74th/ch32v-dev-boards/ch32v203-promicro/docs/ch32v203-promicro.png

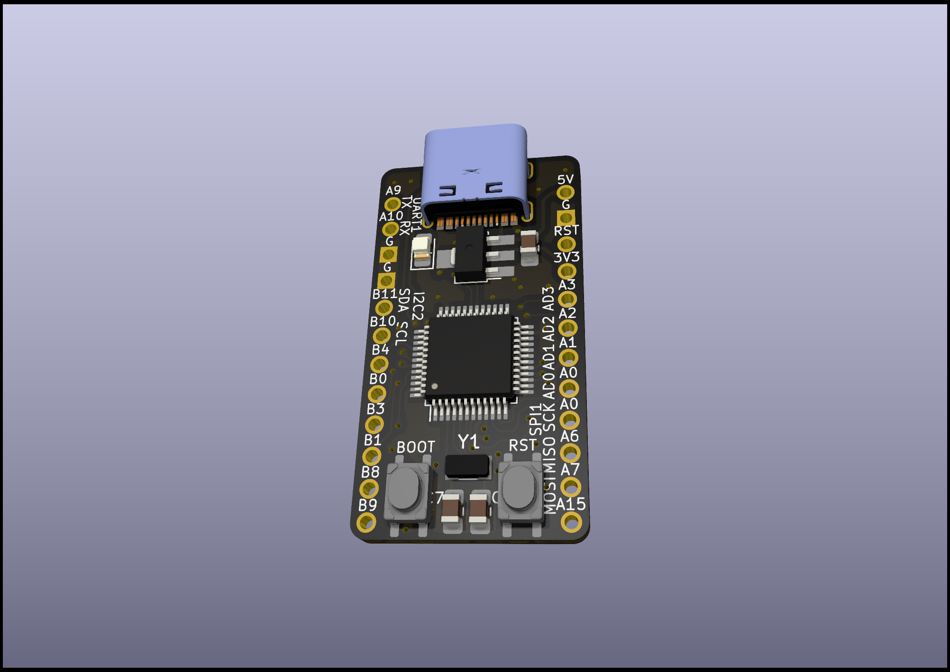
ch32v203-promicro/docs/ch32v203-promicro.png
