74th/ch32v-dev-boards/ch32v203-promicro/docs/switch-science/74th-ch32v203-promicro-like-photo1.jpg

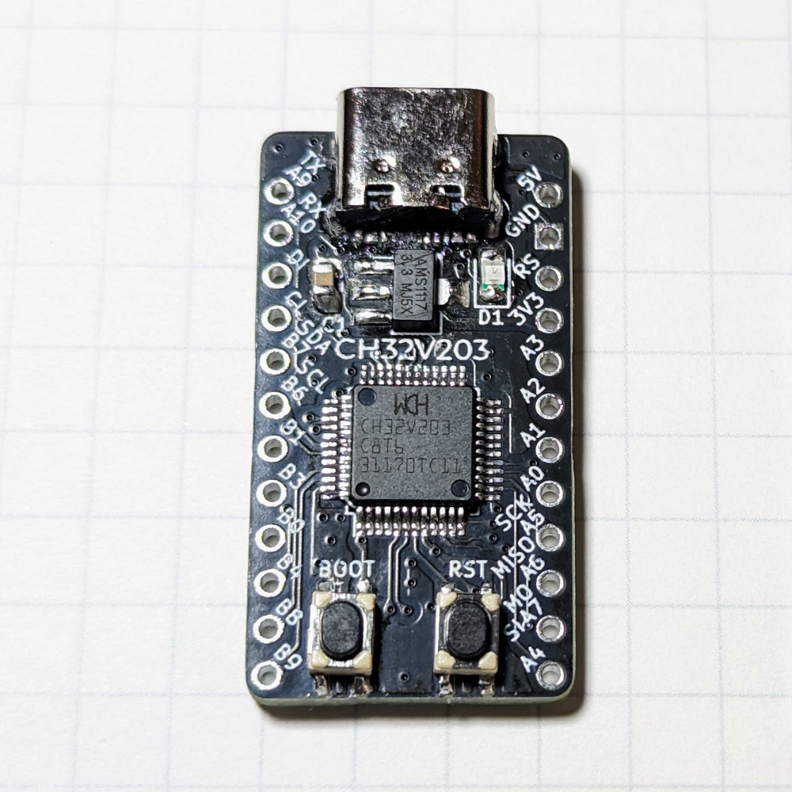
ch32v203-promicro/docs/switch-science/74th-ch32v203-promicro-like-photo1.jpg
