74th/ch32v-dev-boards/ch32v203-promicro/docs/x32micro-v1.1.0-pcb.pdf

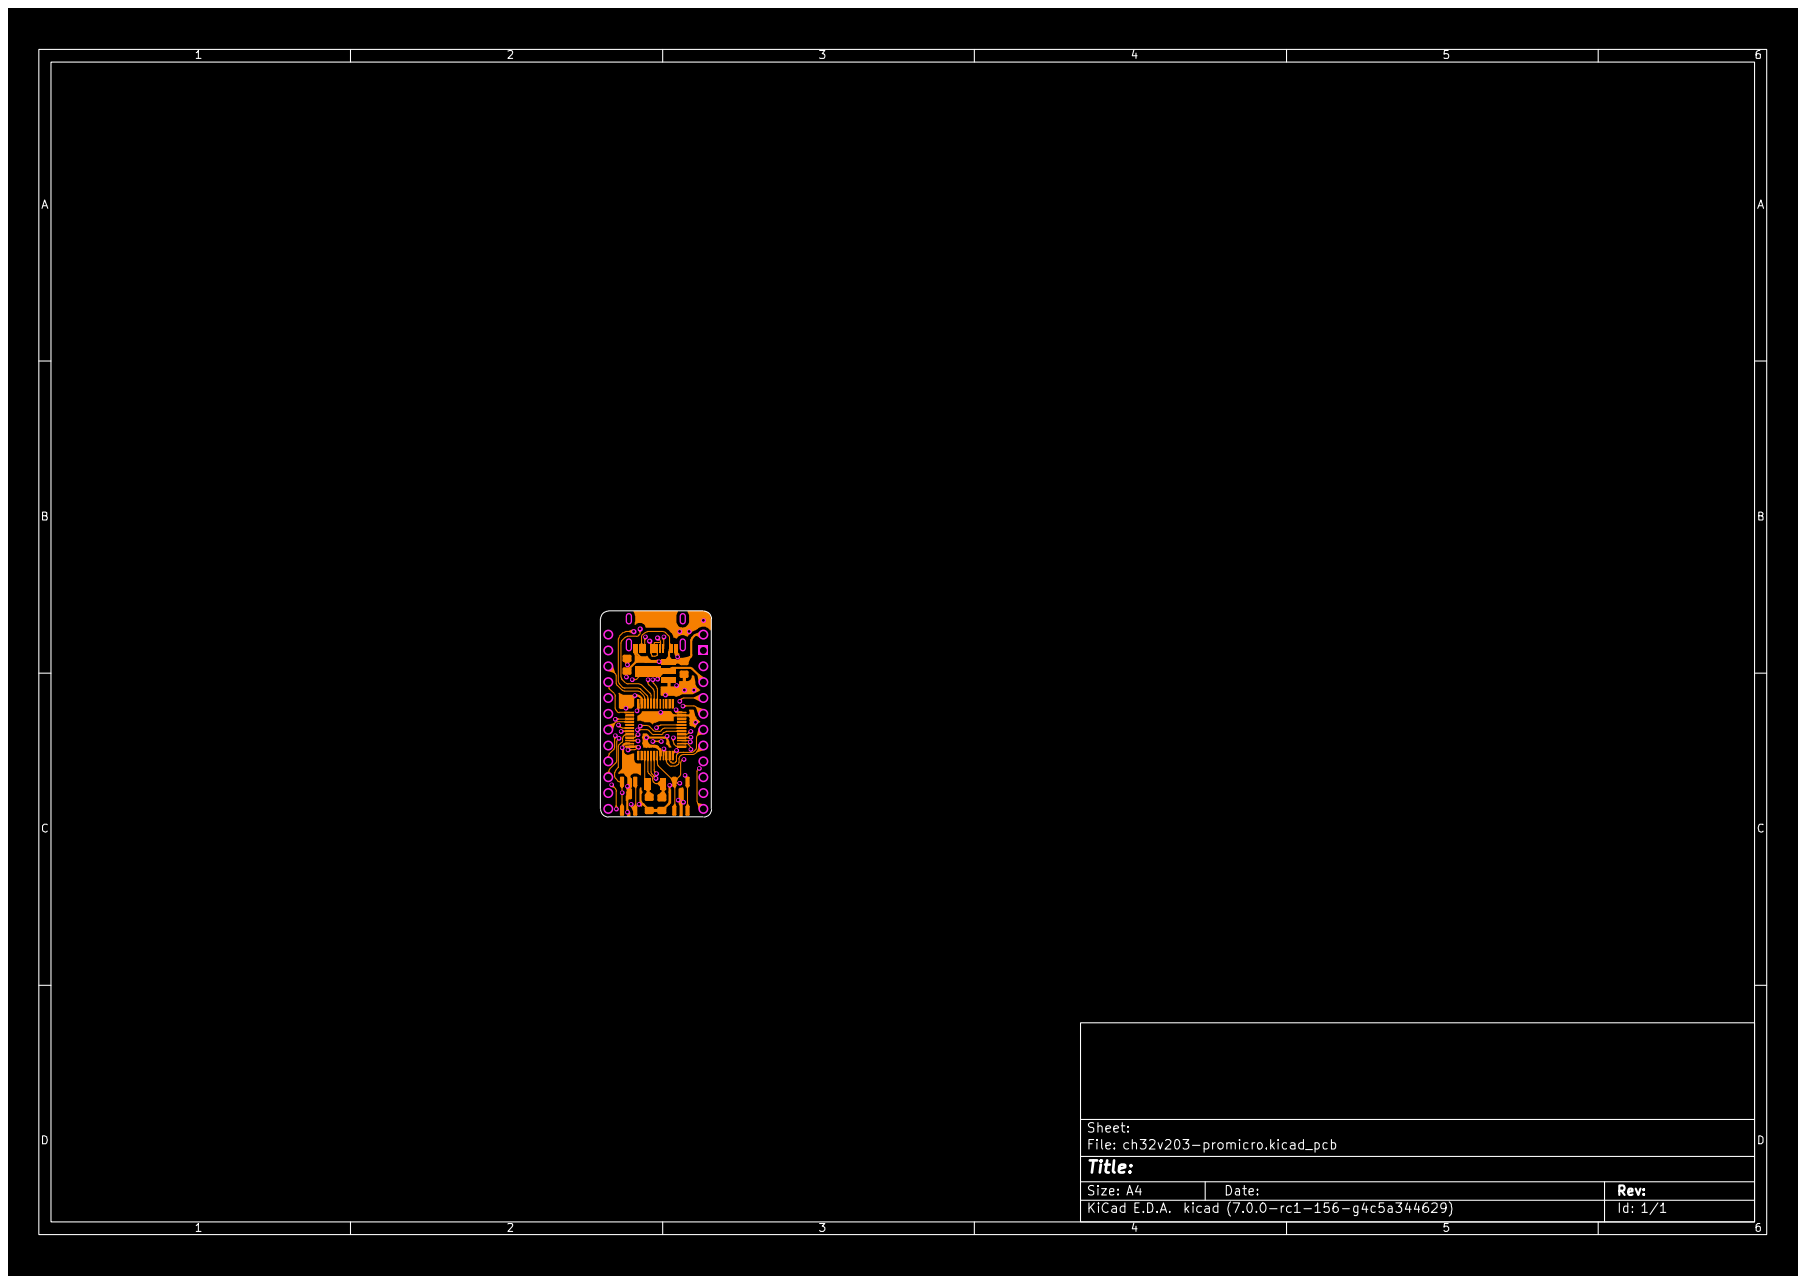
[picture p43: page 1]

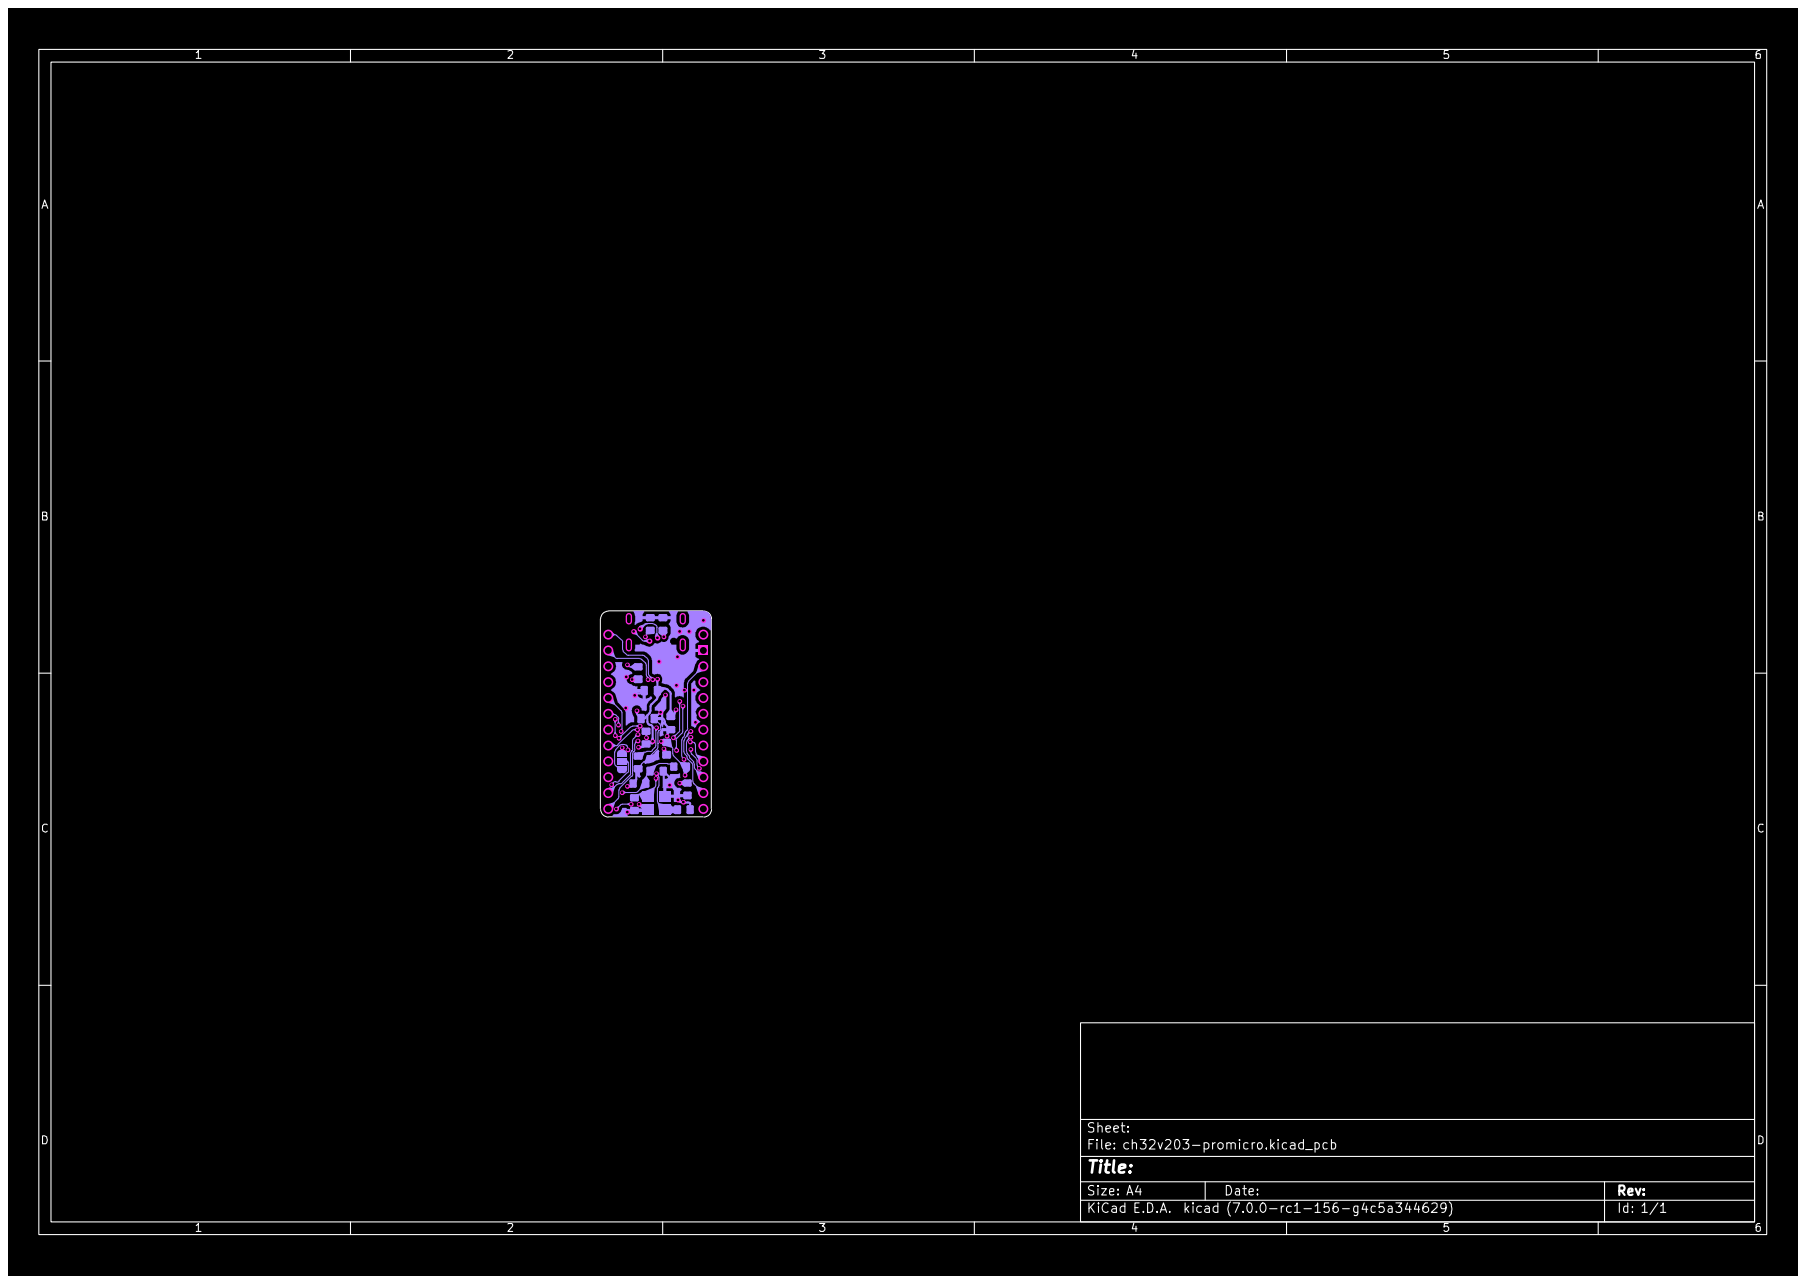
[picture p44: page 2]

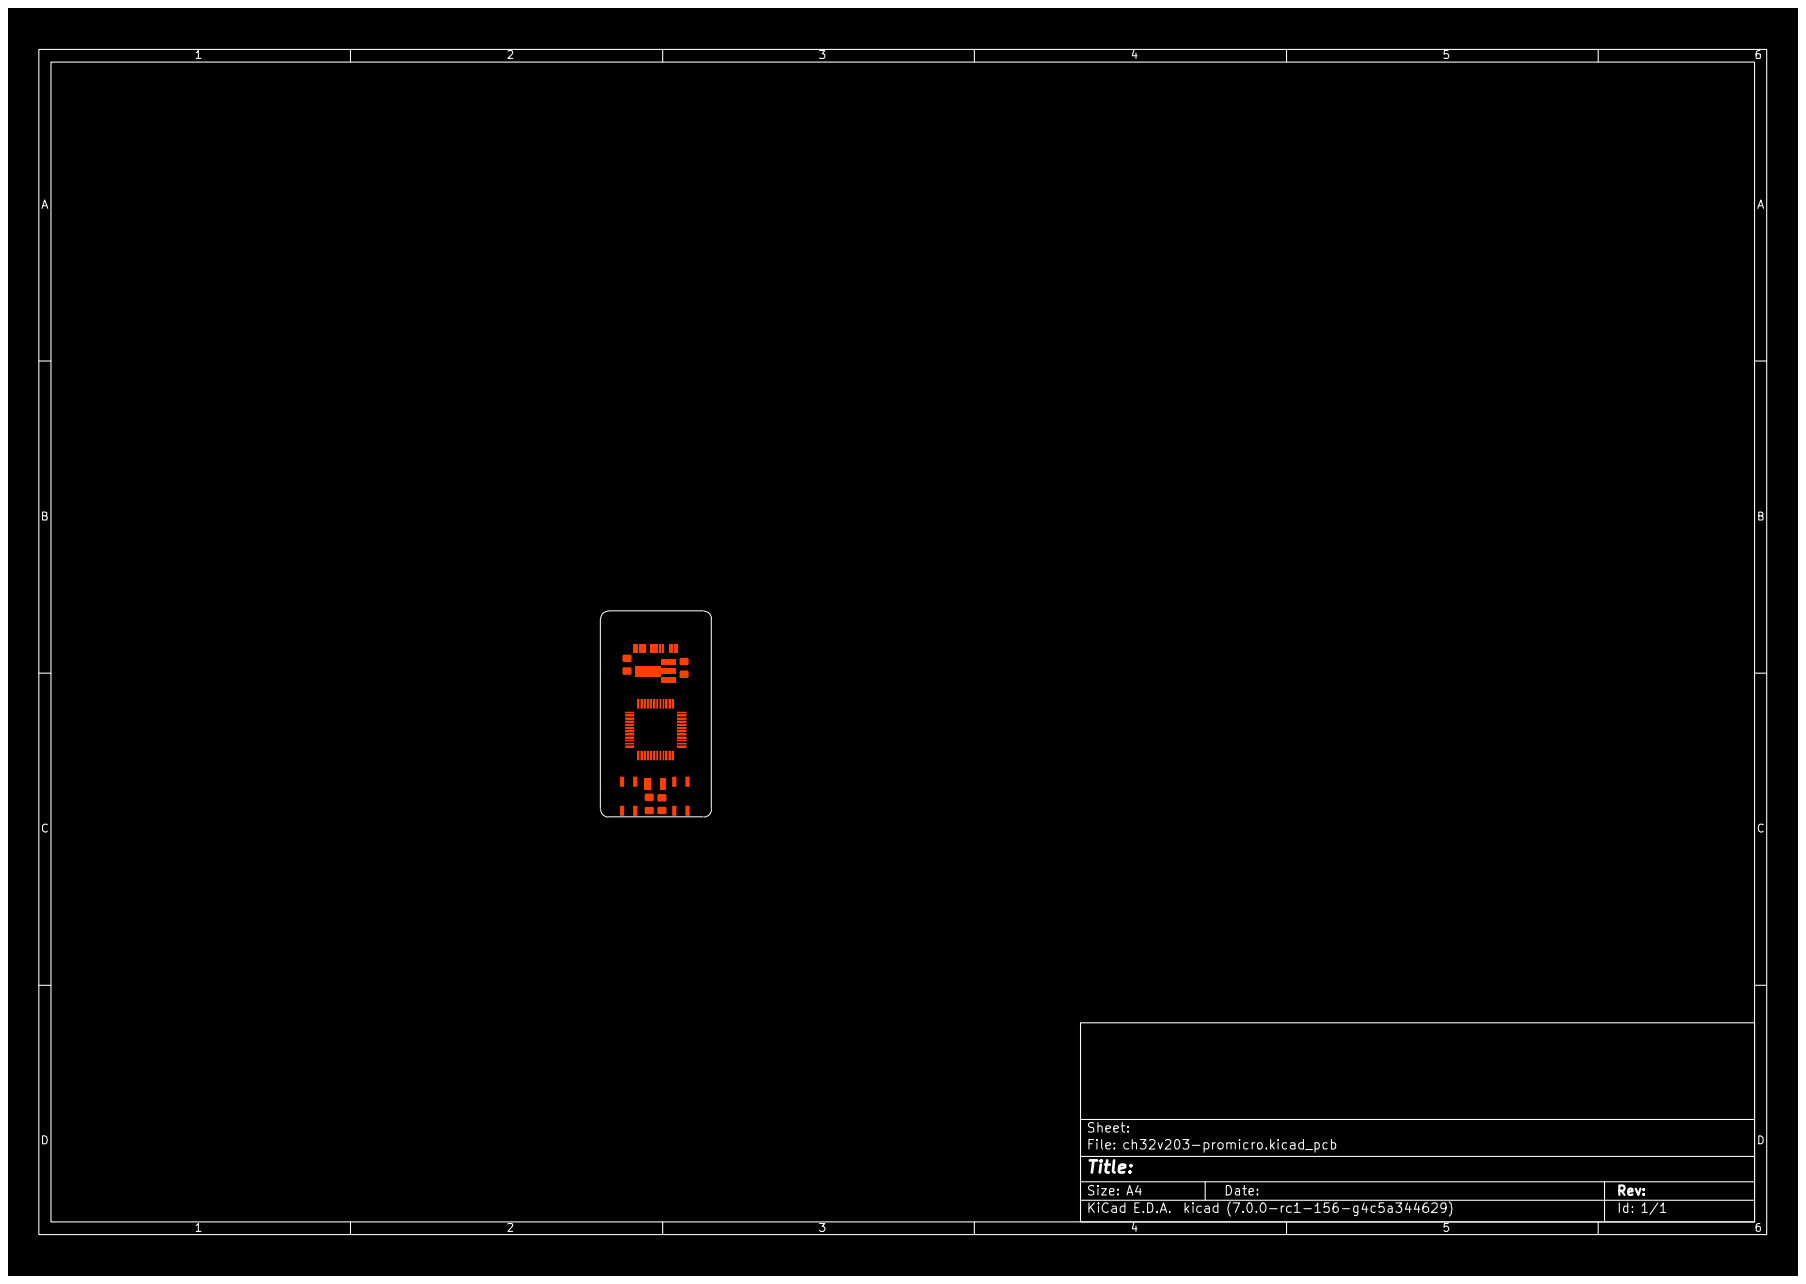
[picture p45: page 3]

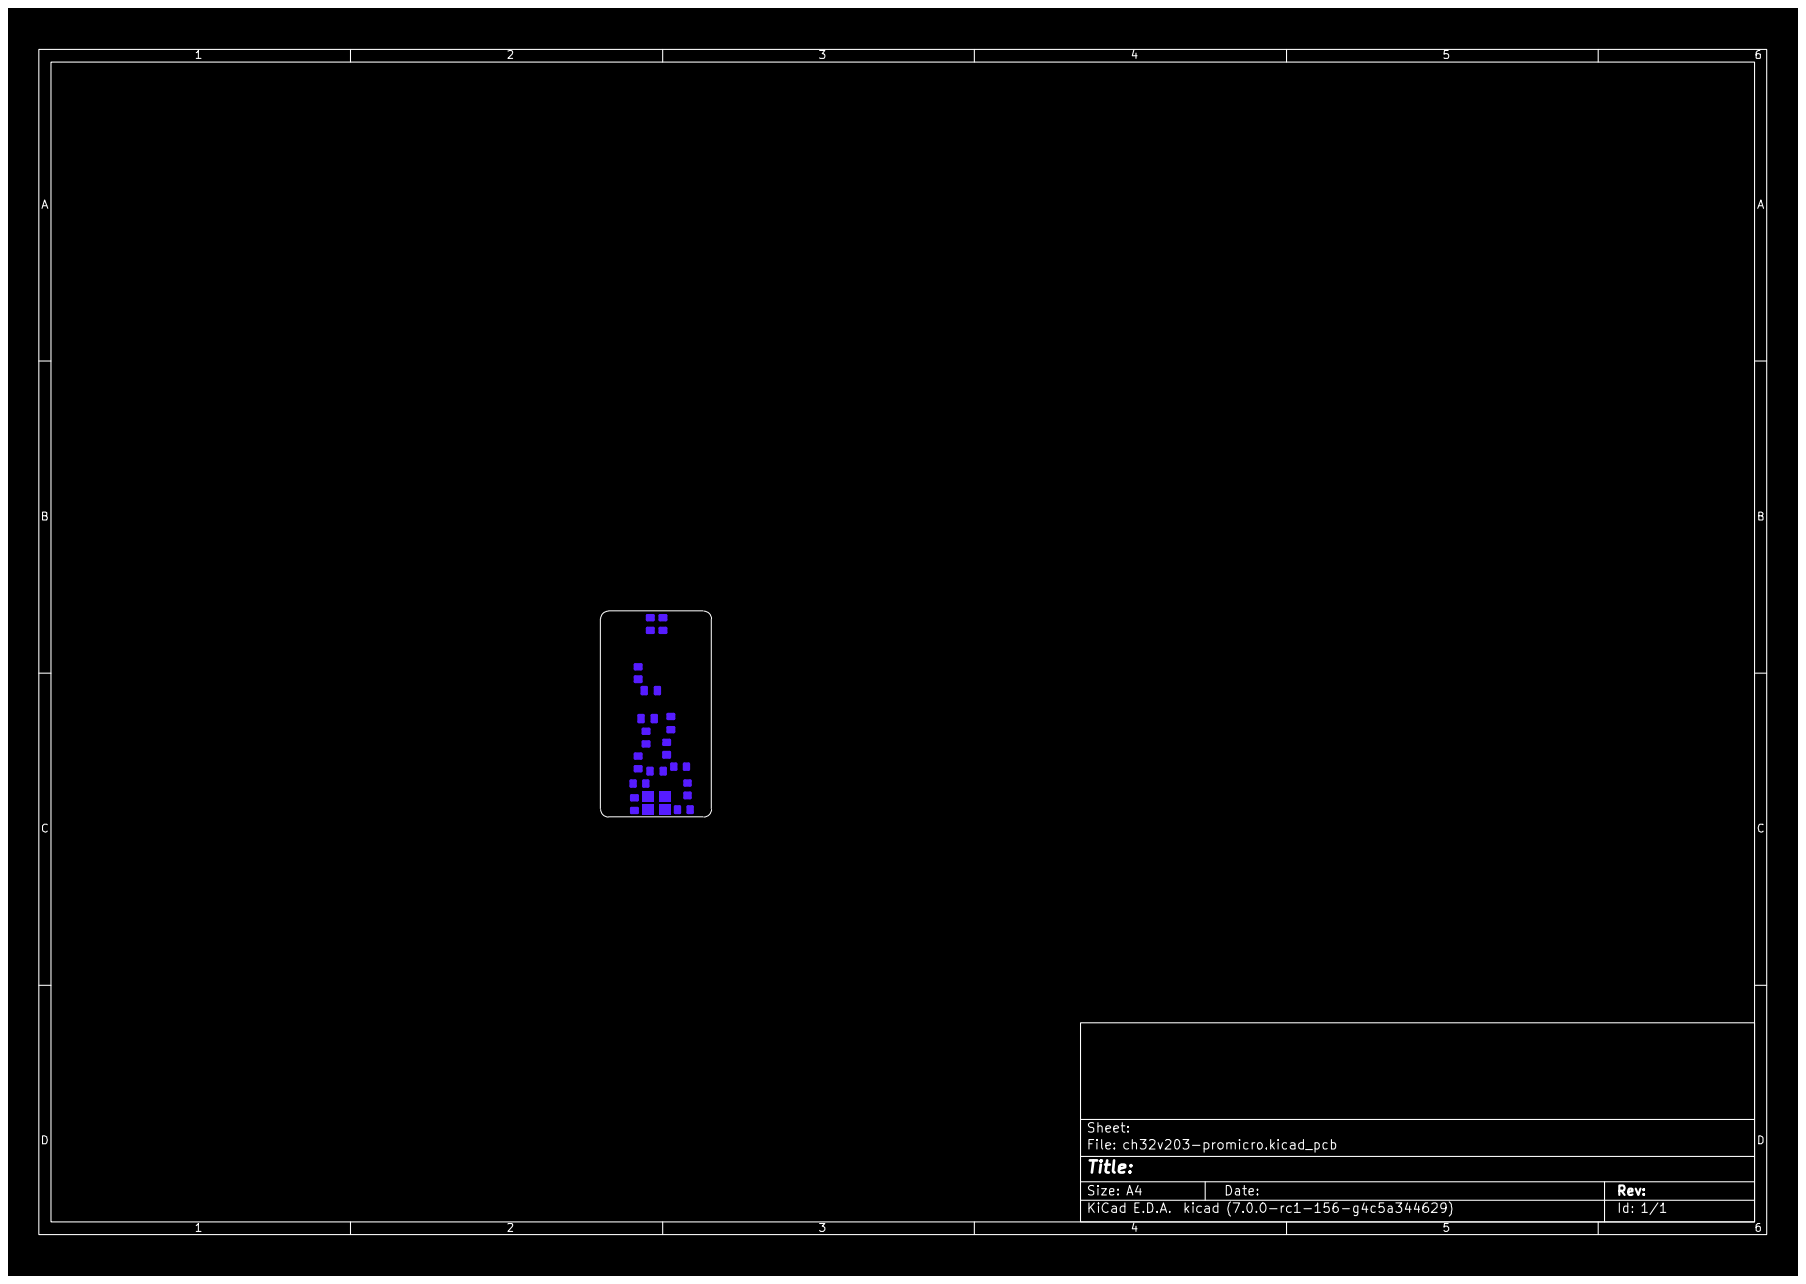
[picture p46: page 4]

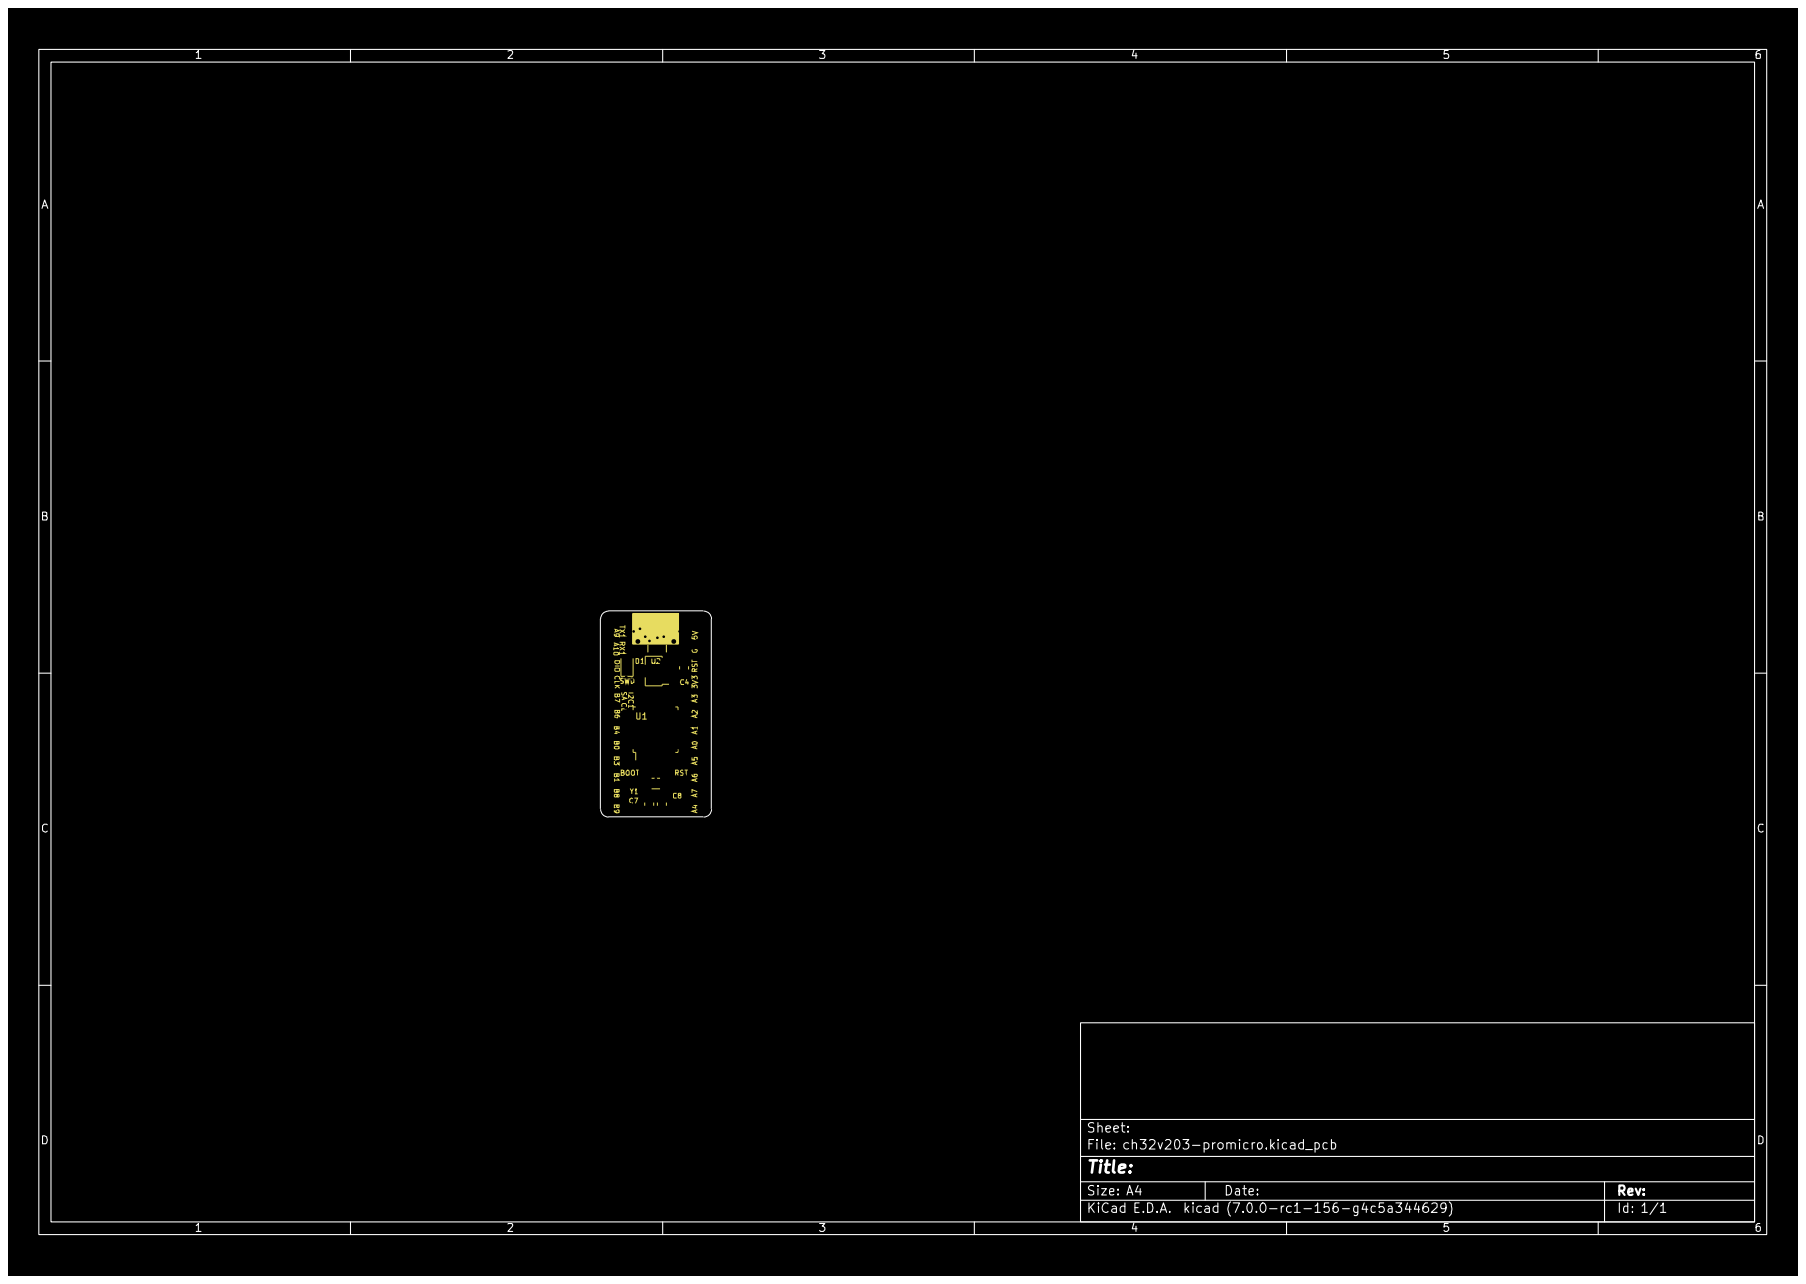
[picture p47: page 5]

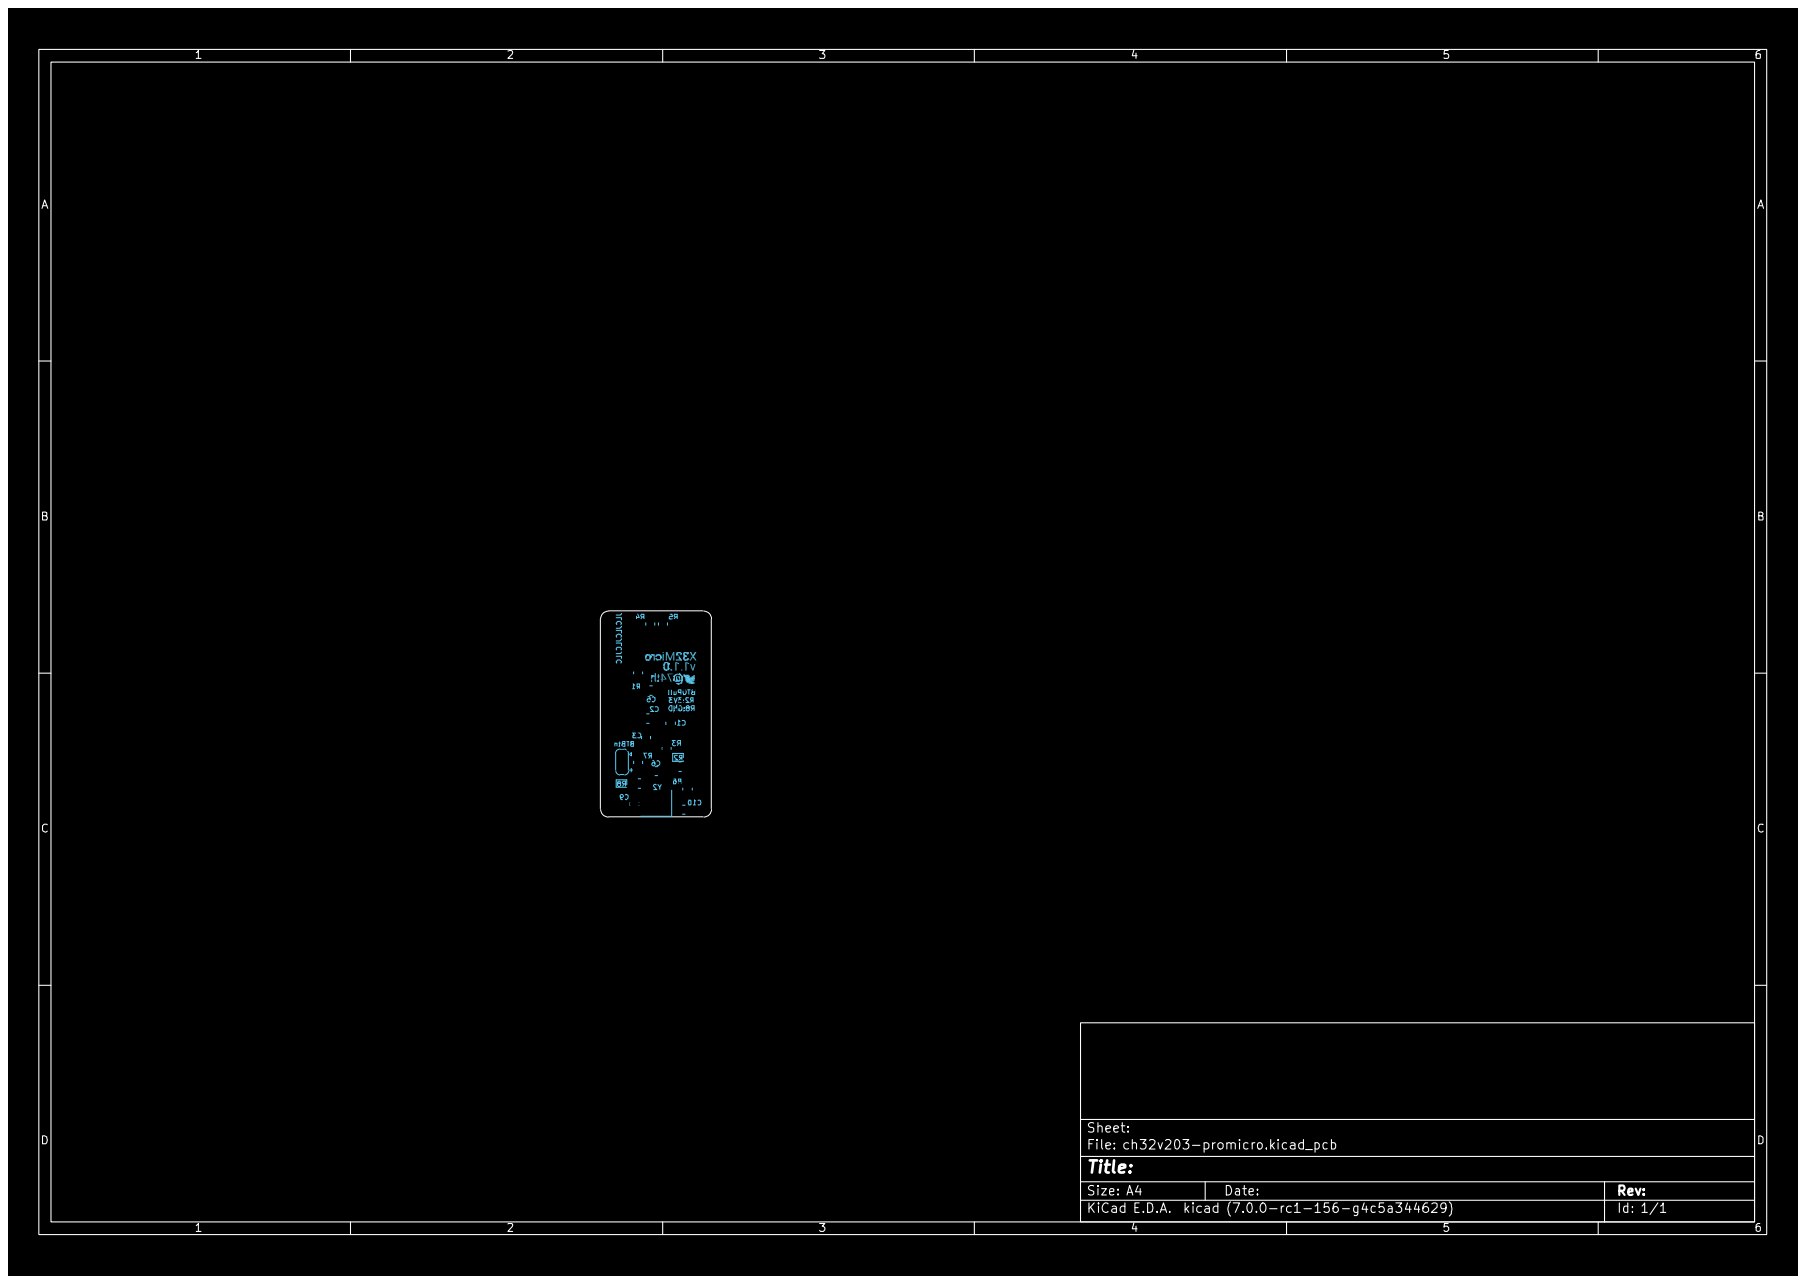
[picture p48: page 6]

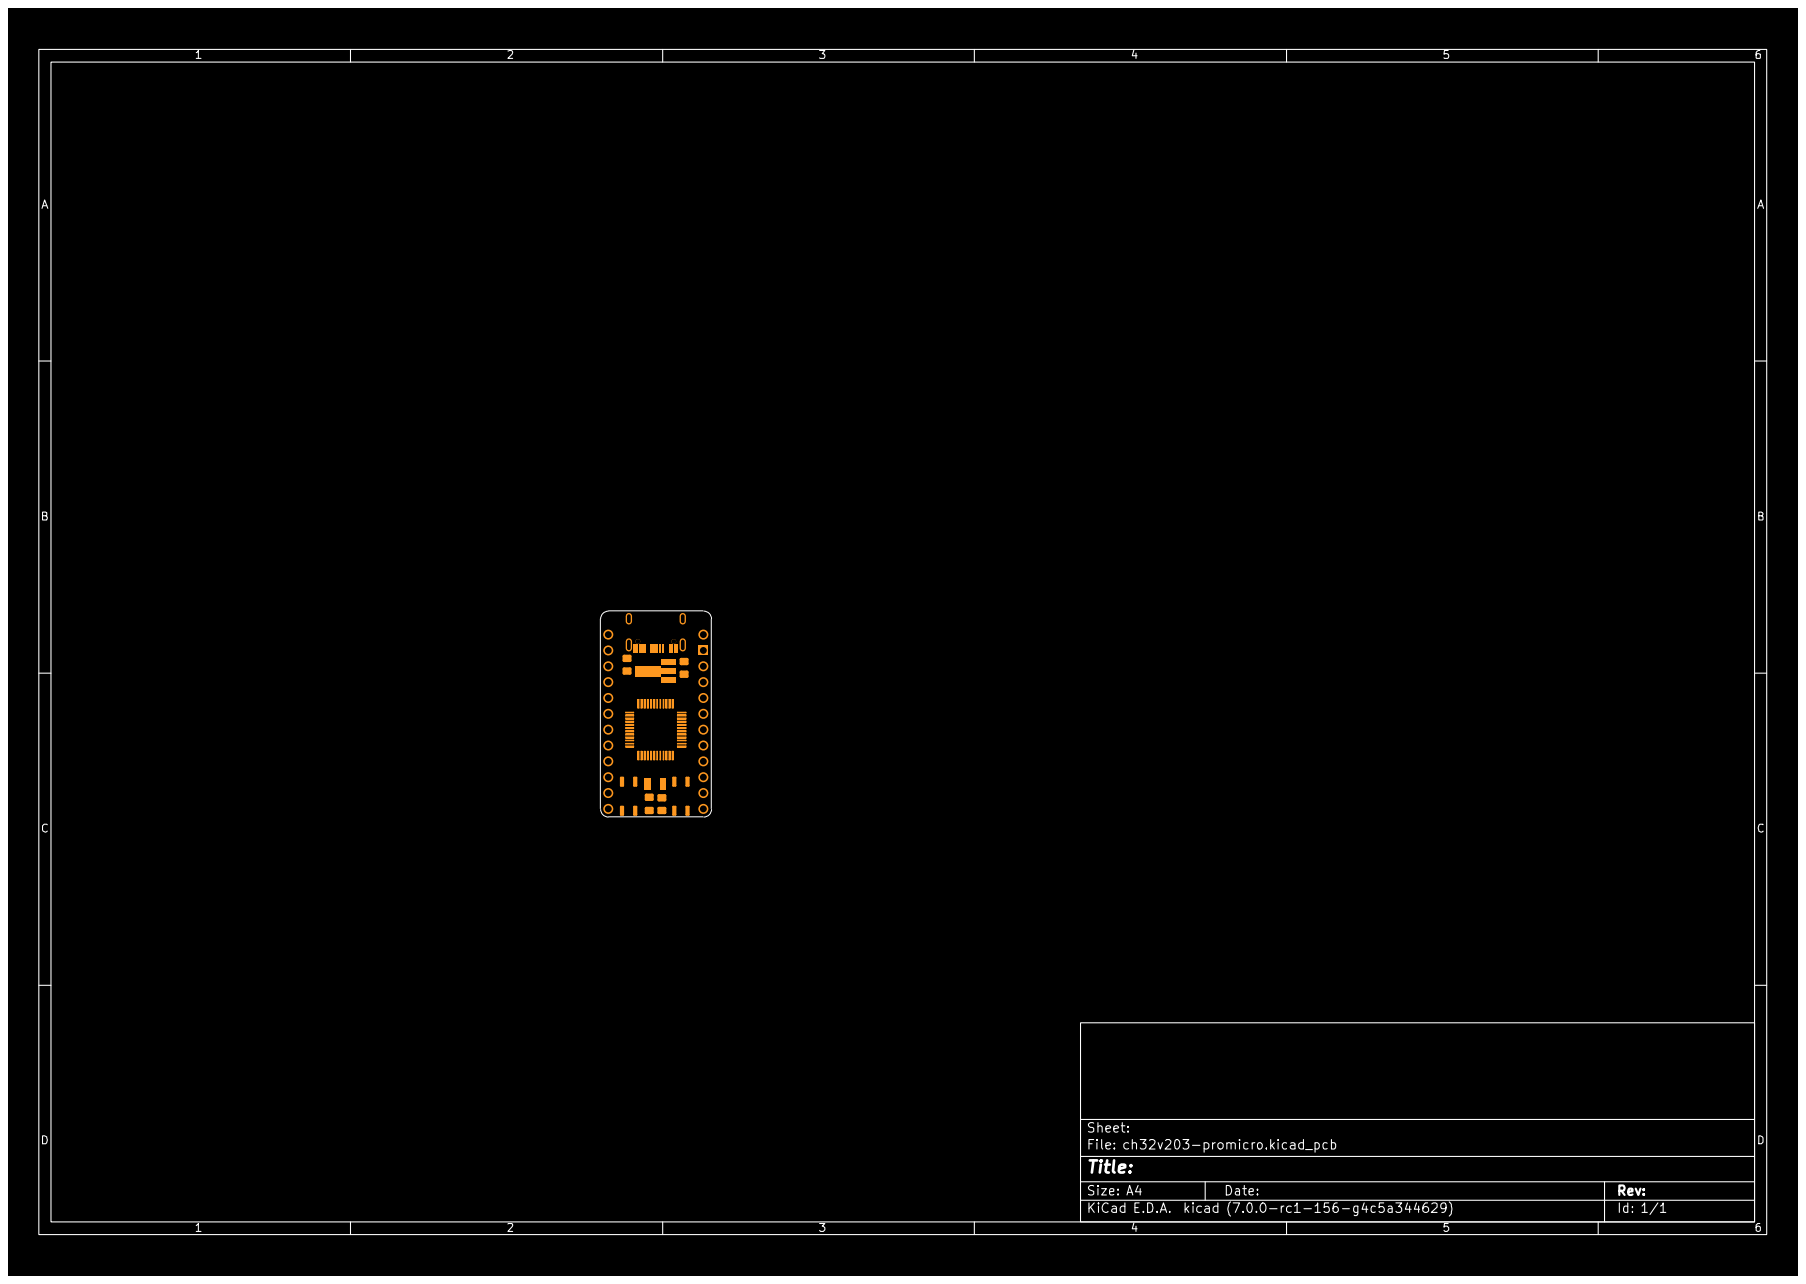
[picture p49: page 7]

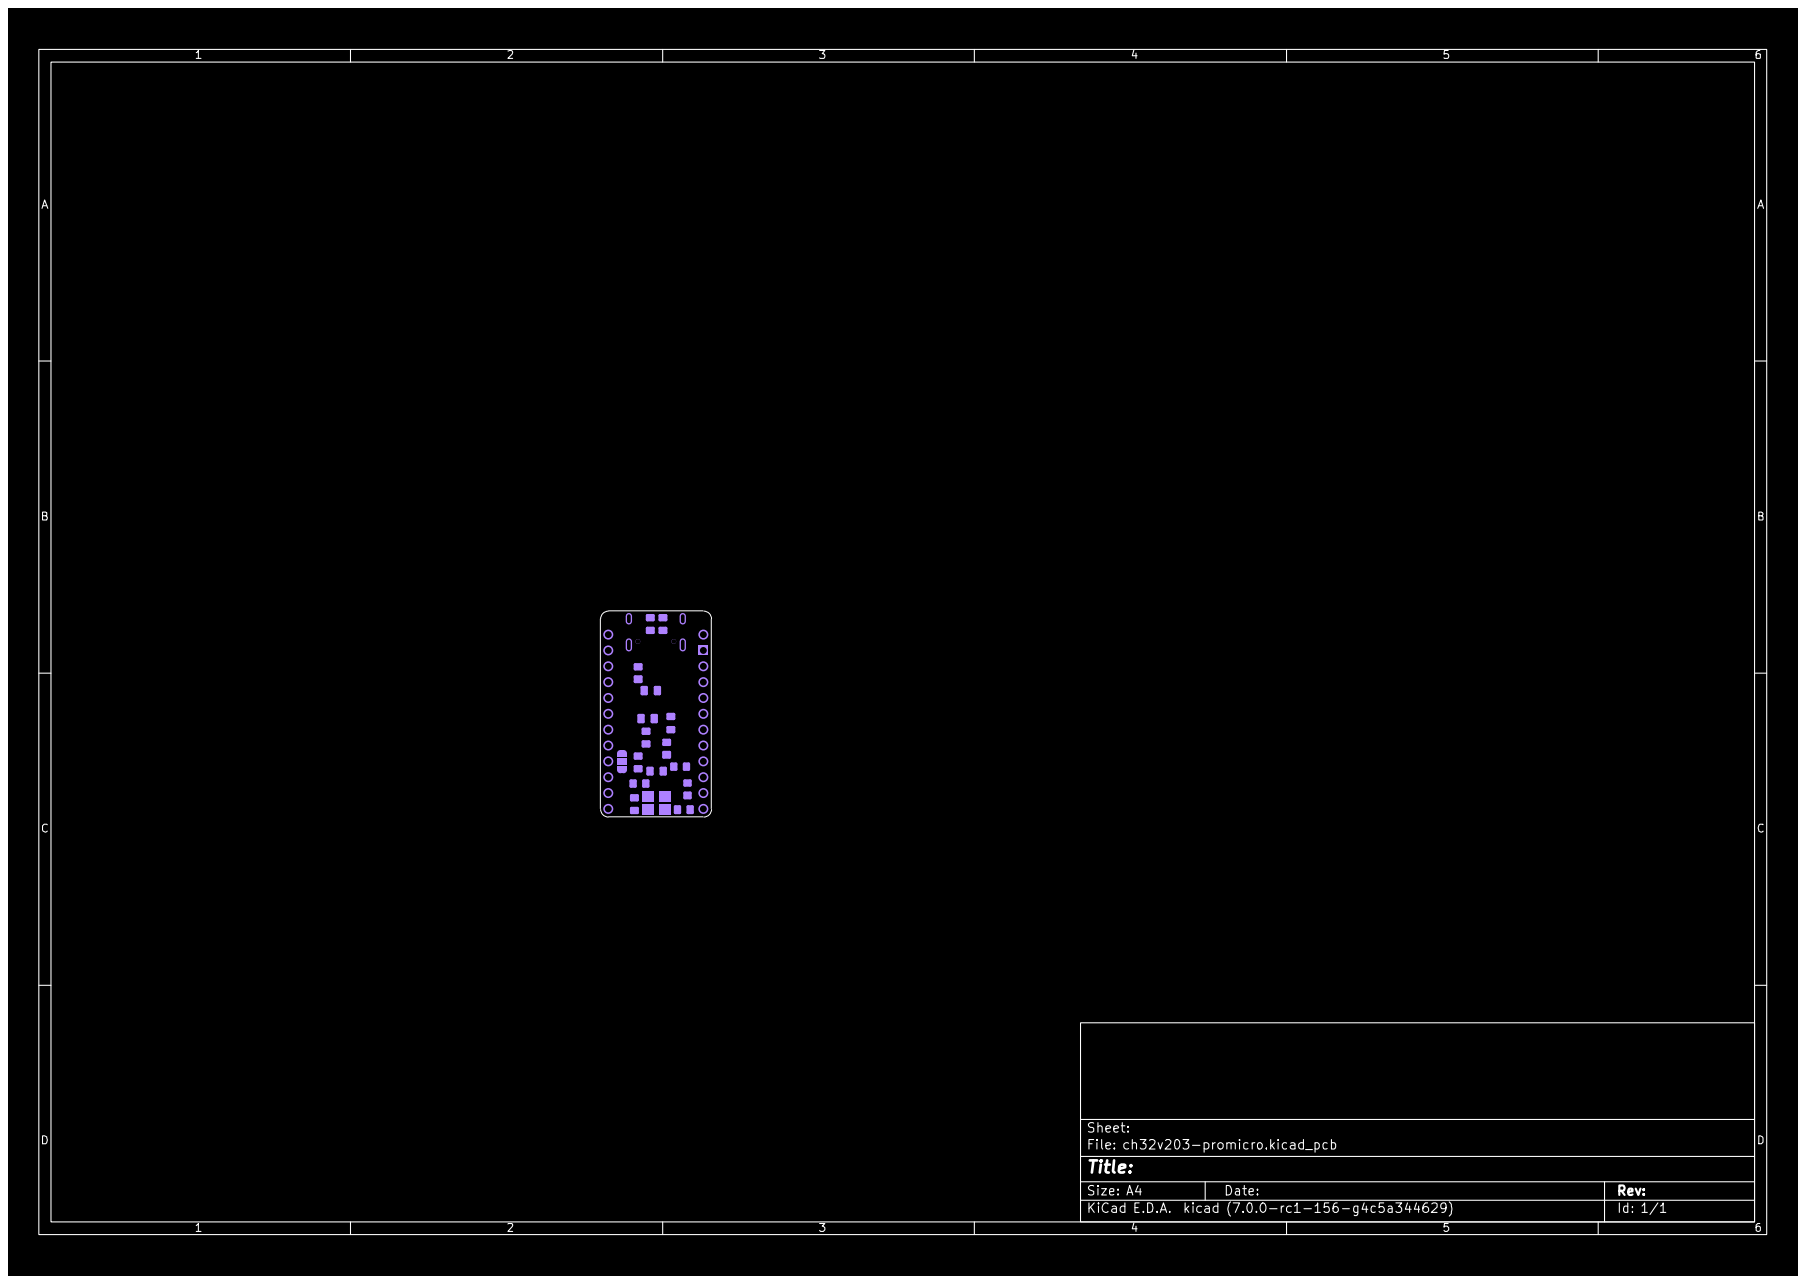
[picture p50: page 8]
