74th/ch32v-dev-boards/ch32v203-promicro/docs/x32micro-v1.1.0-semantics.pdf

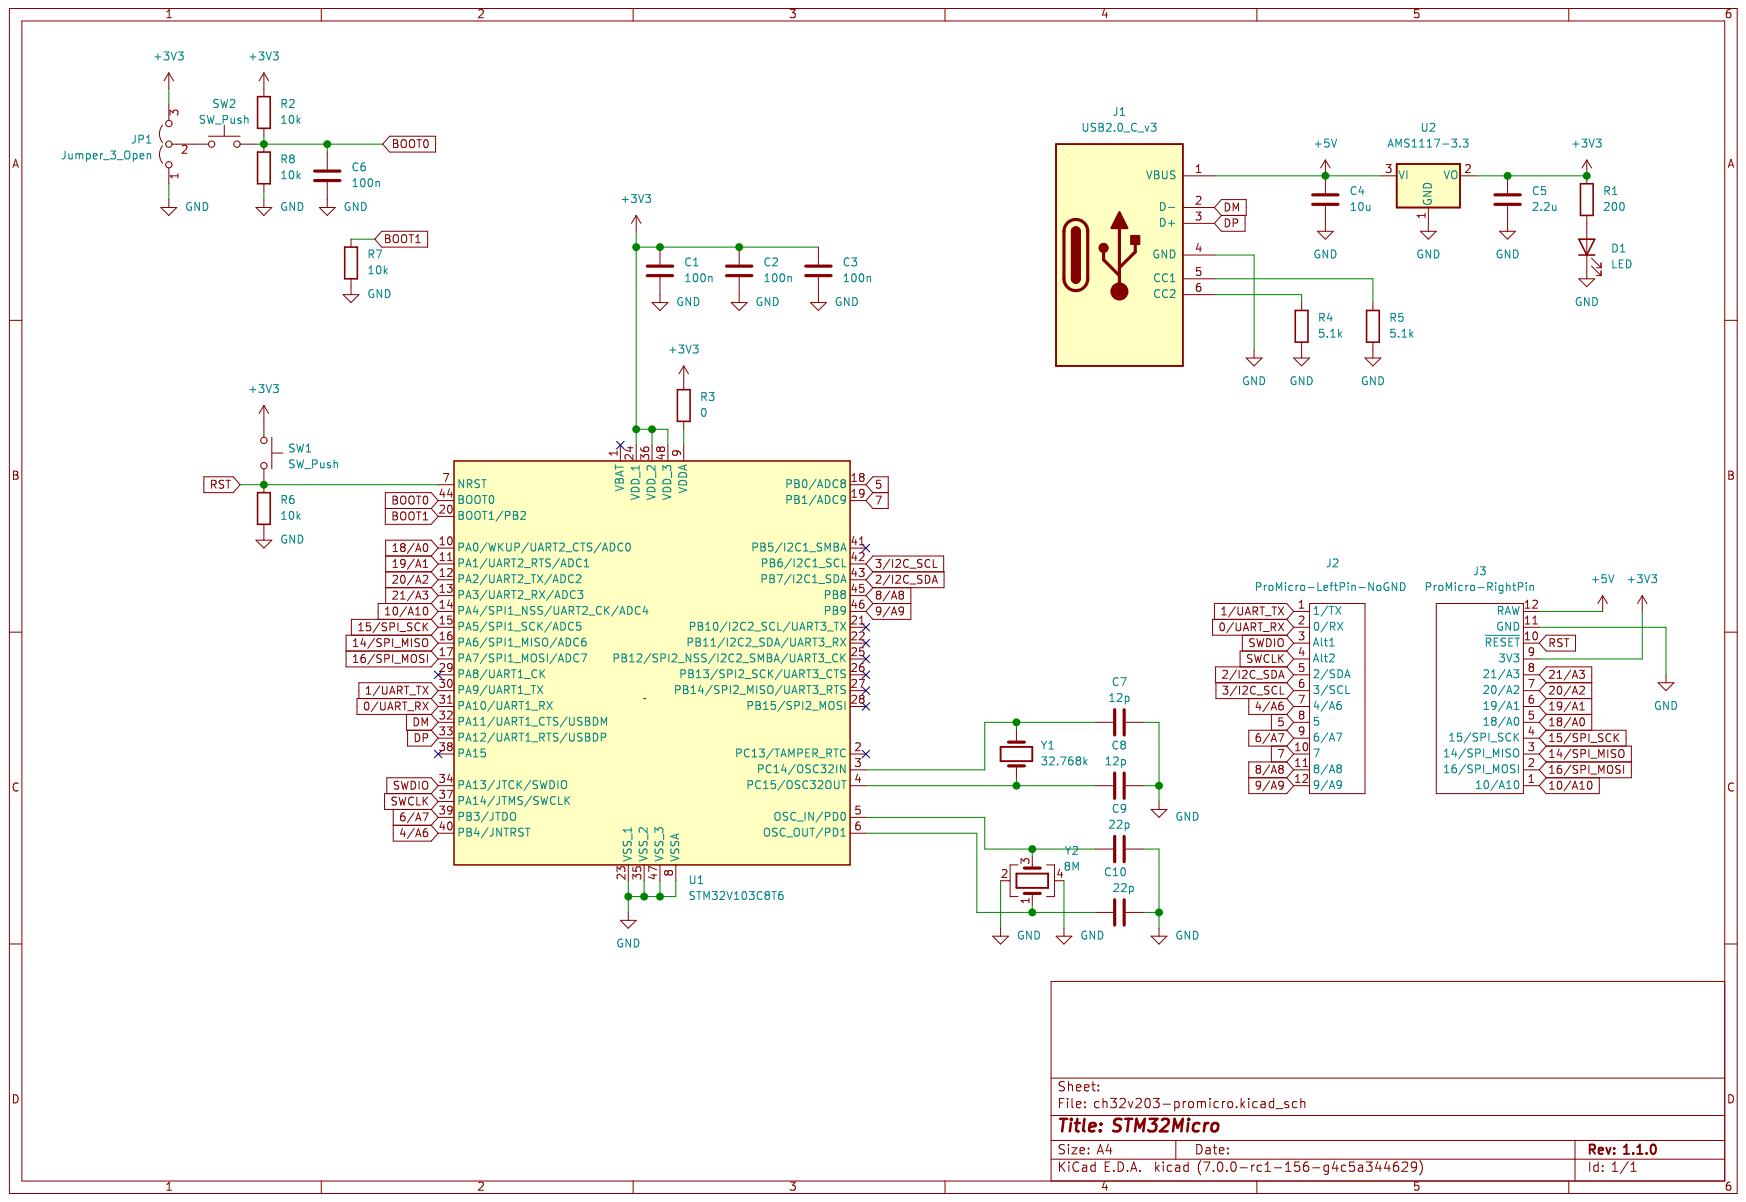
[picture p51: page 1]
