74th/ch32v-dev-boards/ch32v203-promicro/docs/ch32v203-promicro-v1.0.0-pcb.pdf

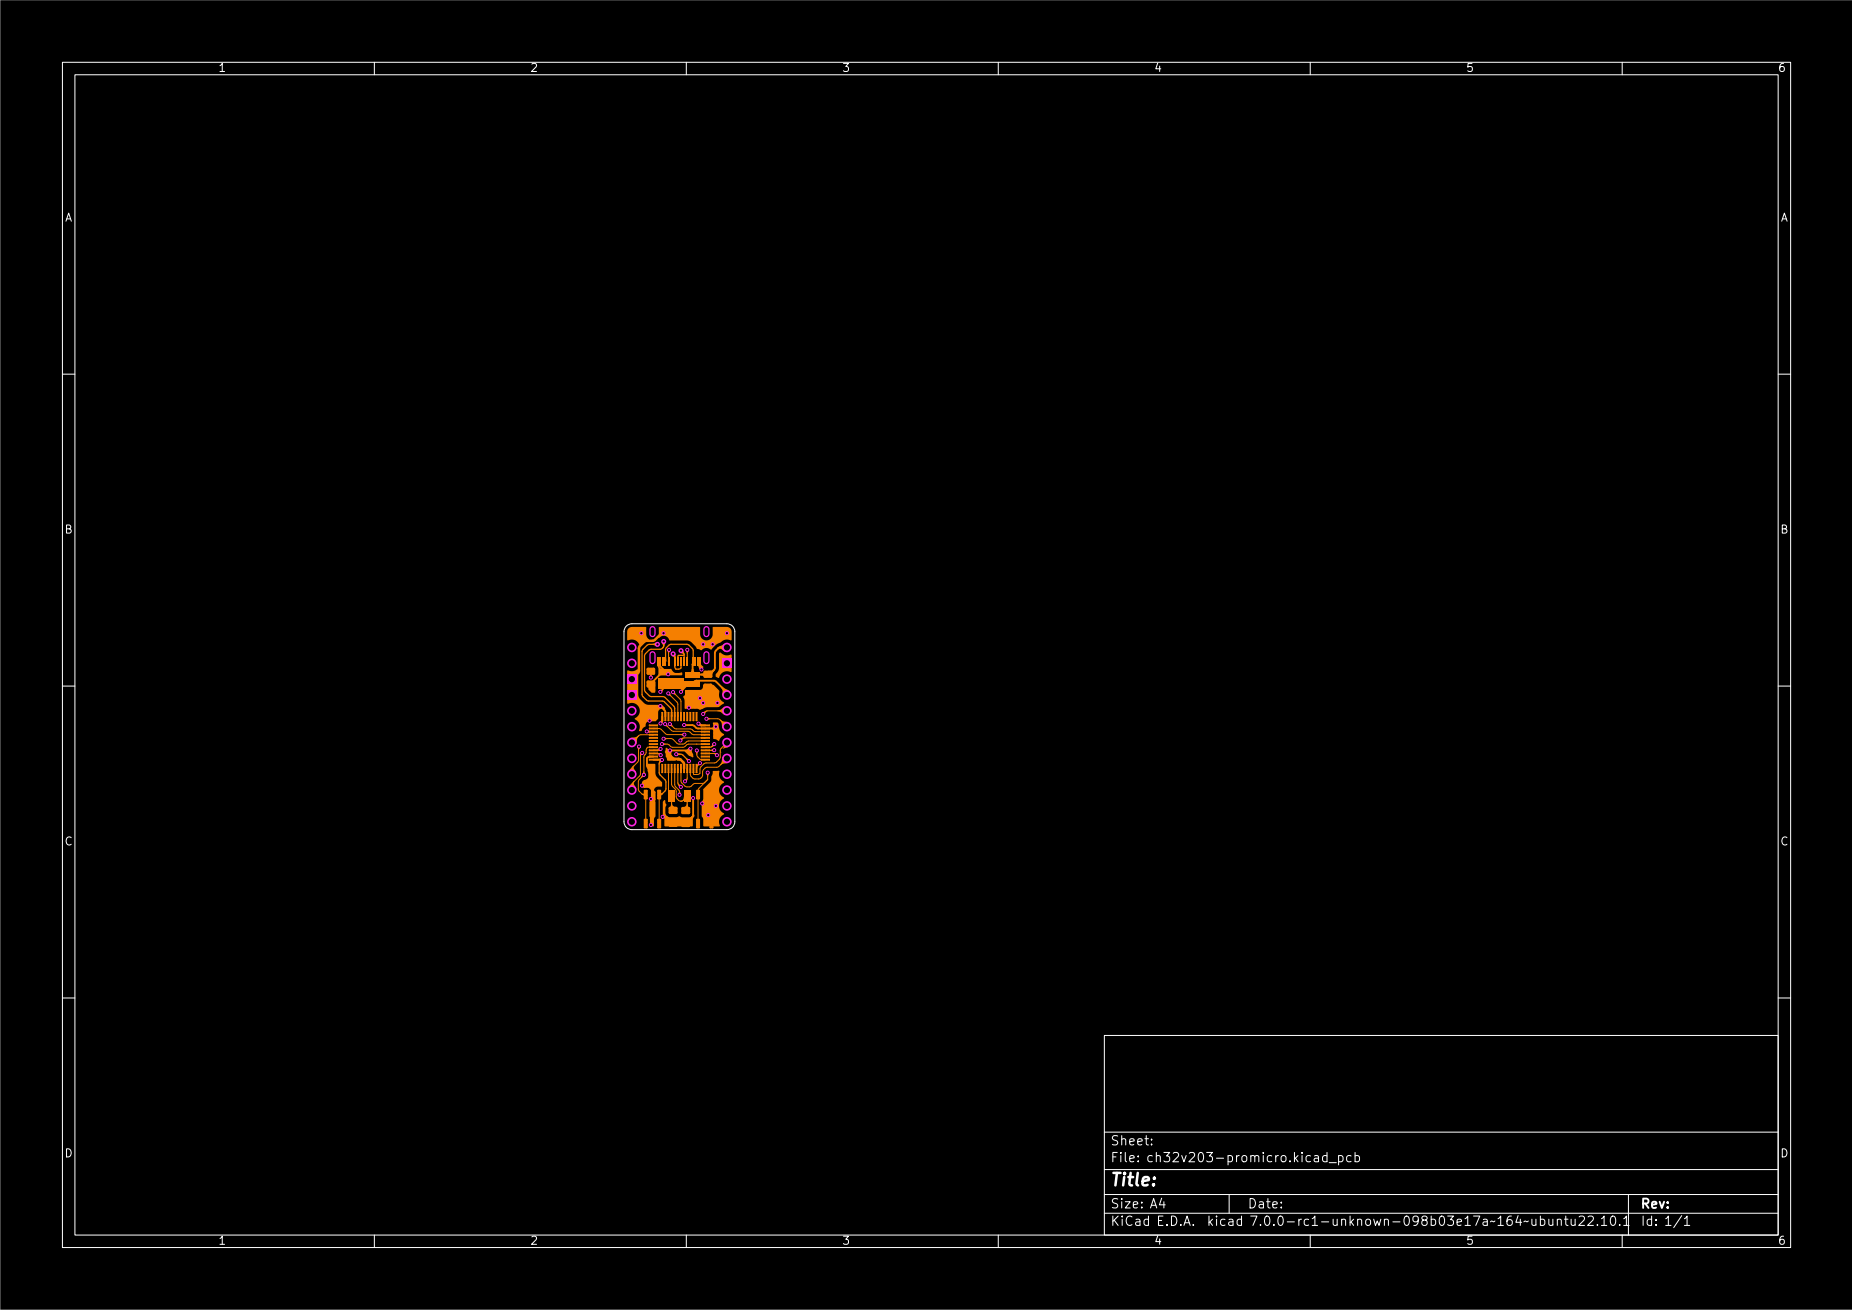
[picture p52: page 1]

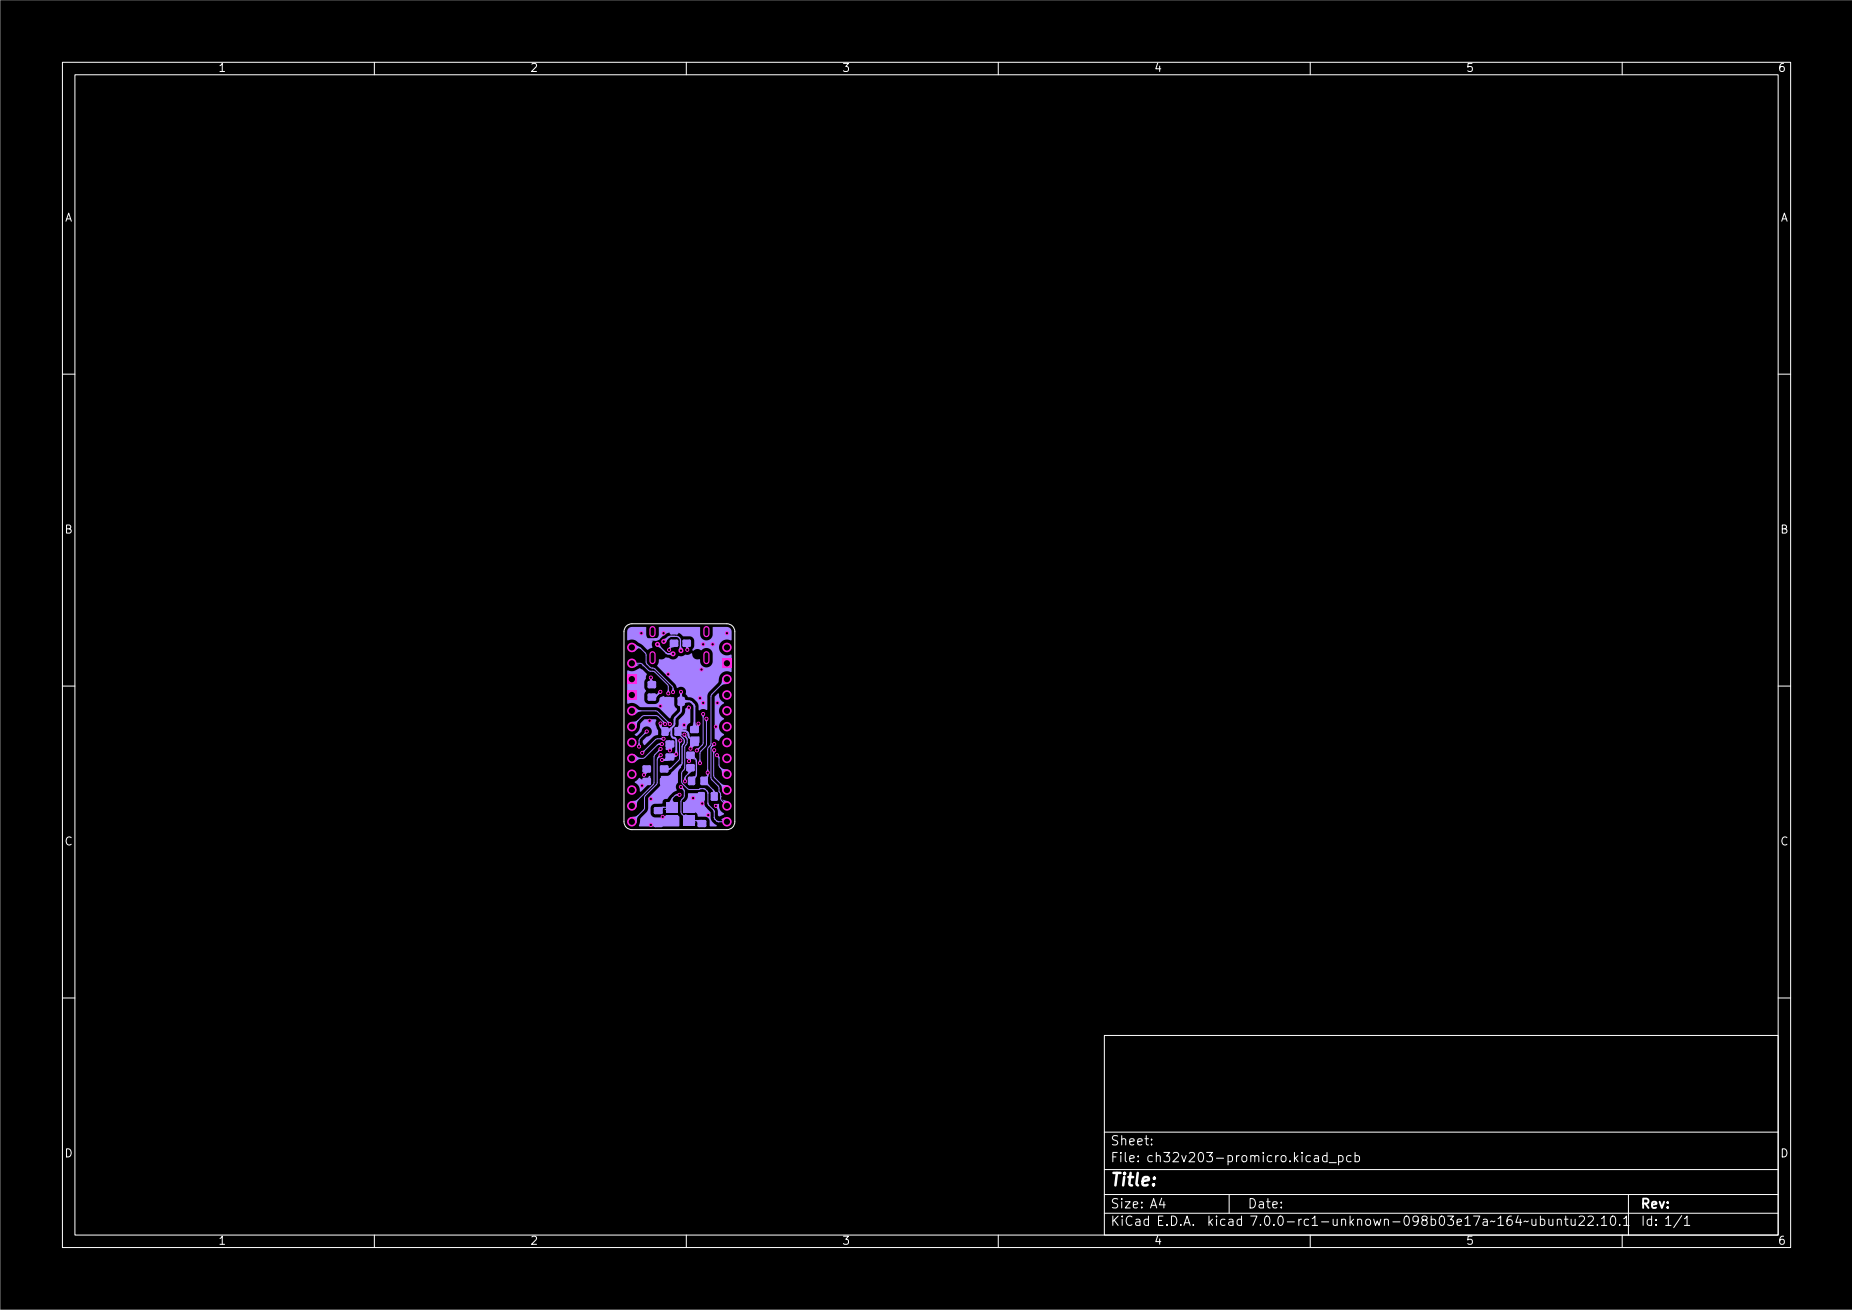
[picture p53: page 2]

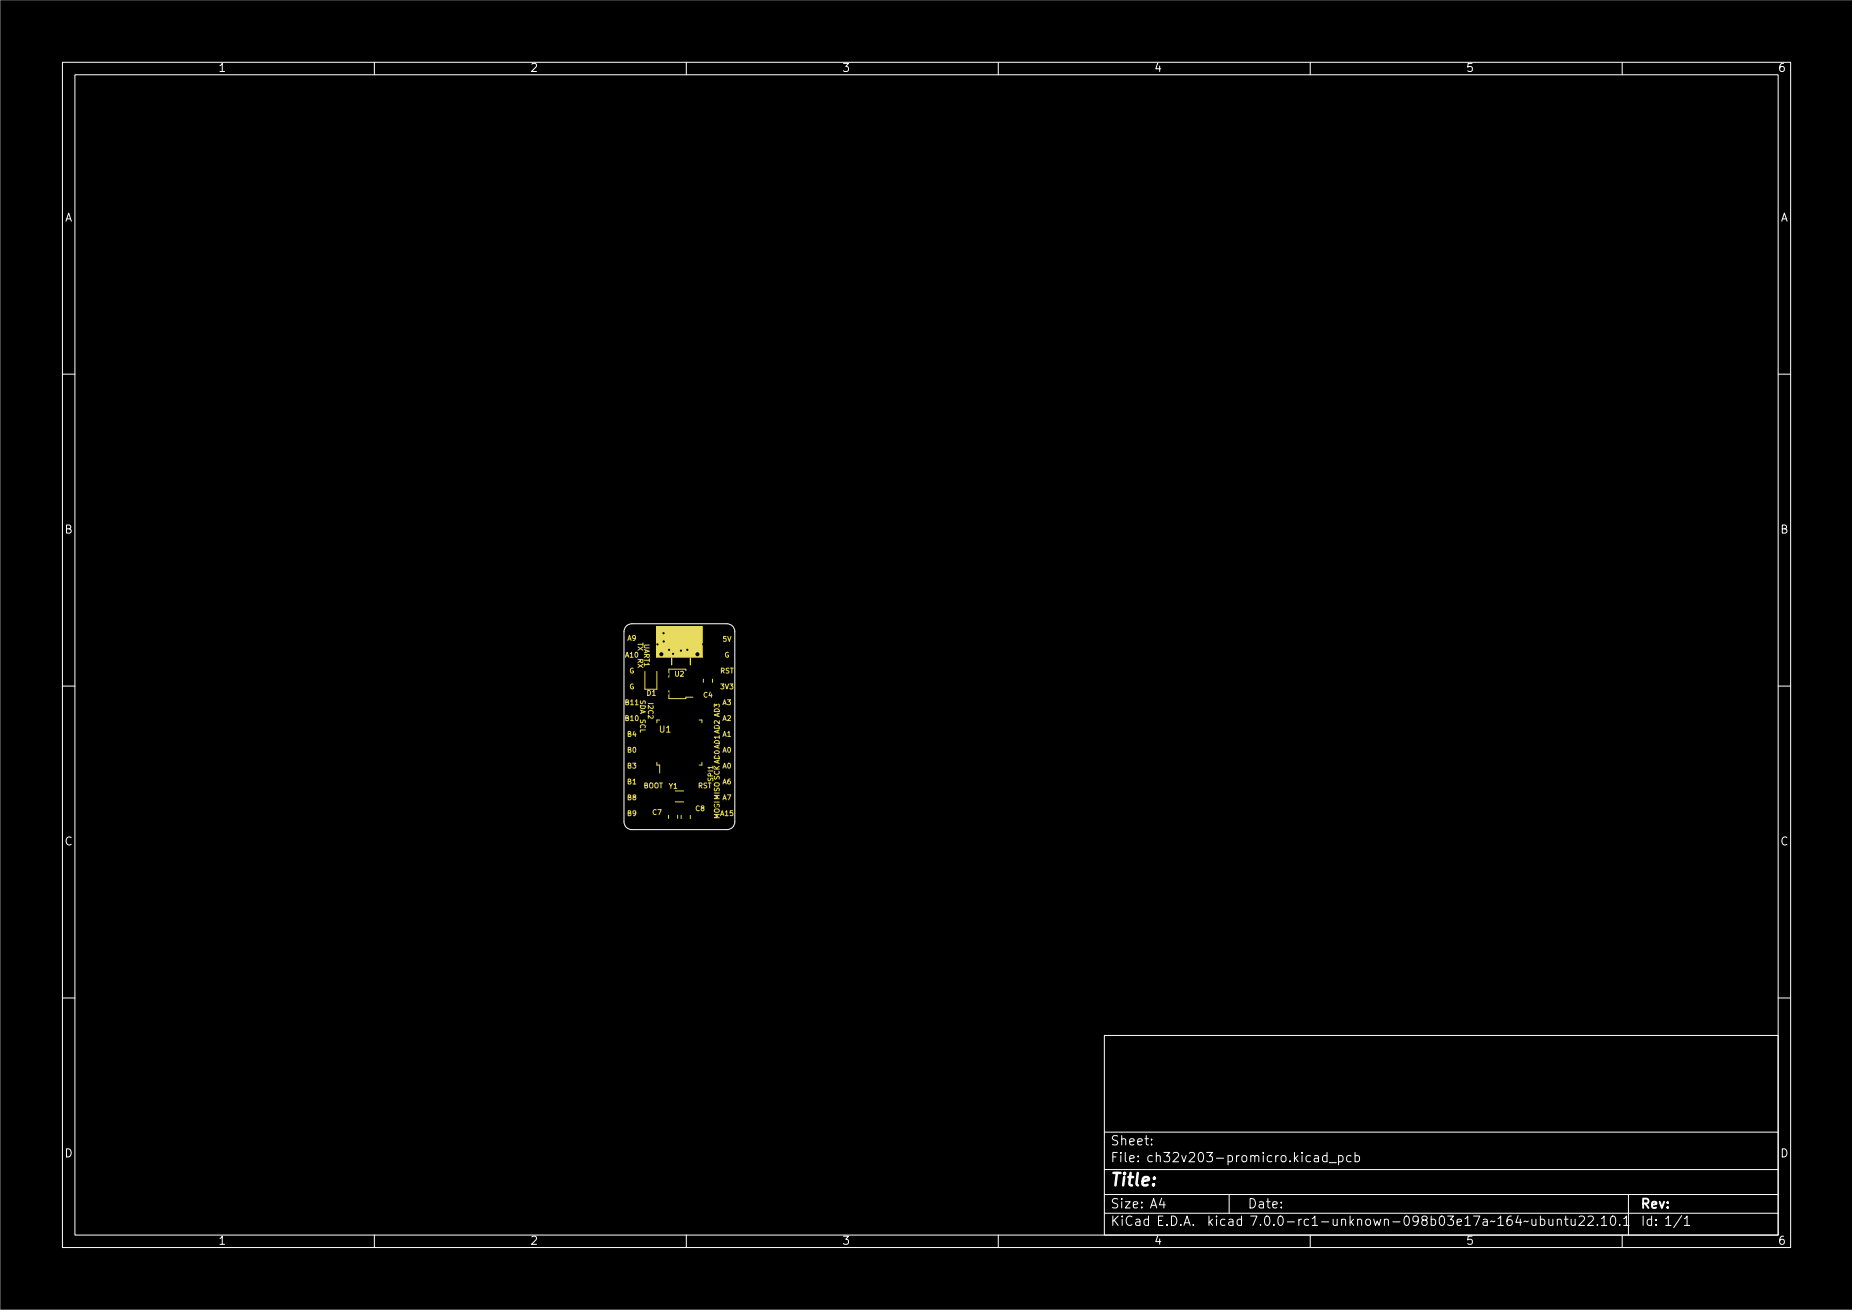
[picture p54: page 3]

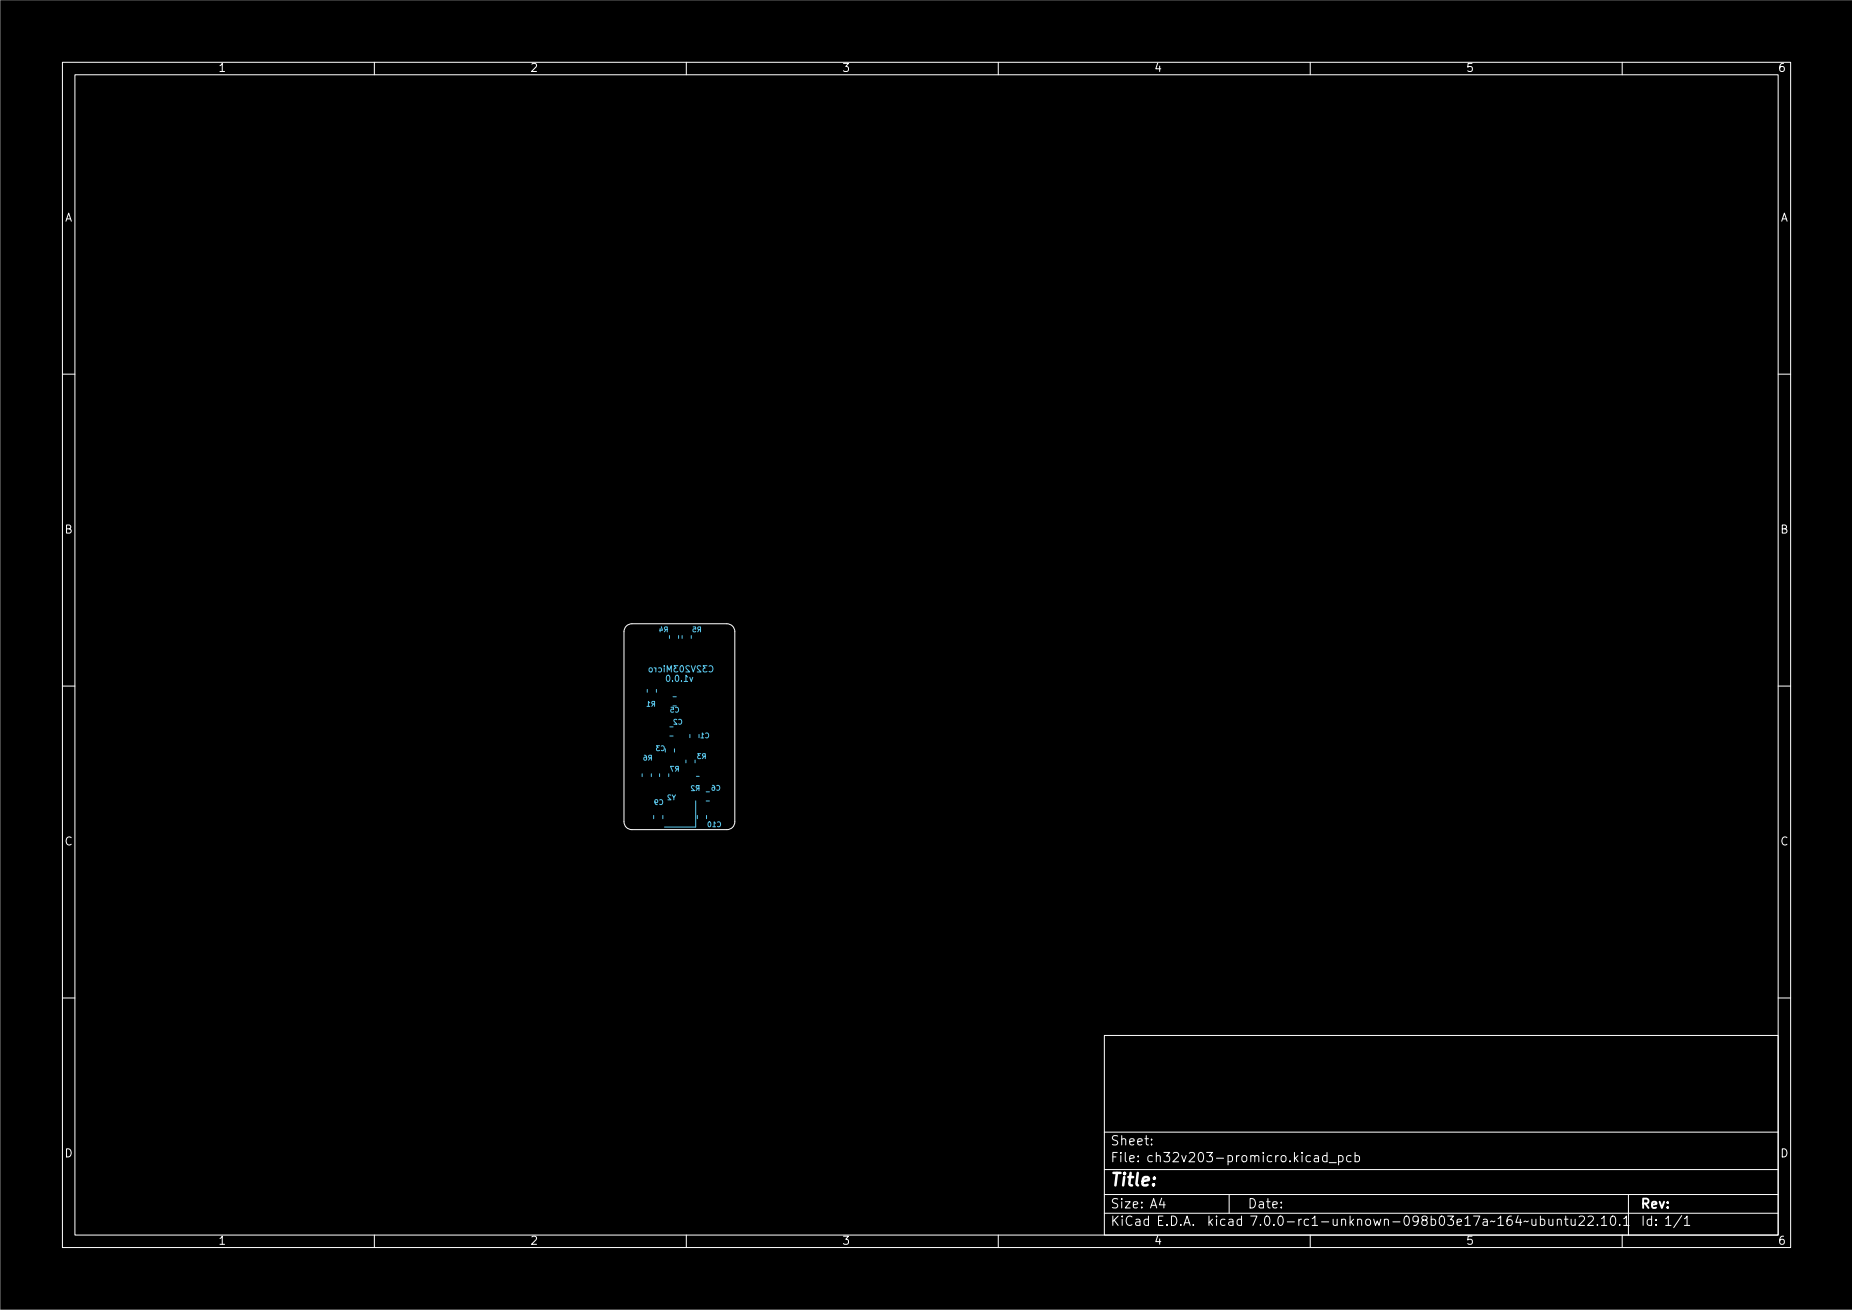
[picture p55: page 4]

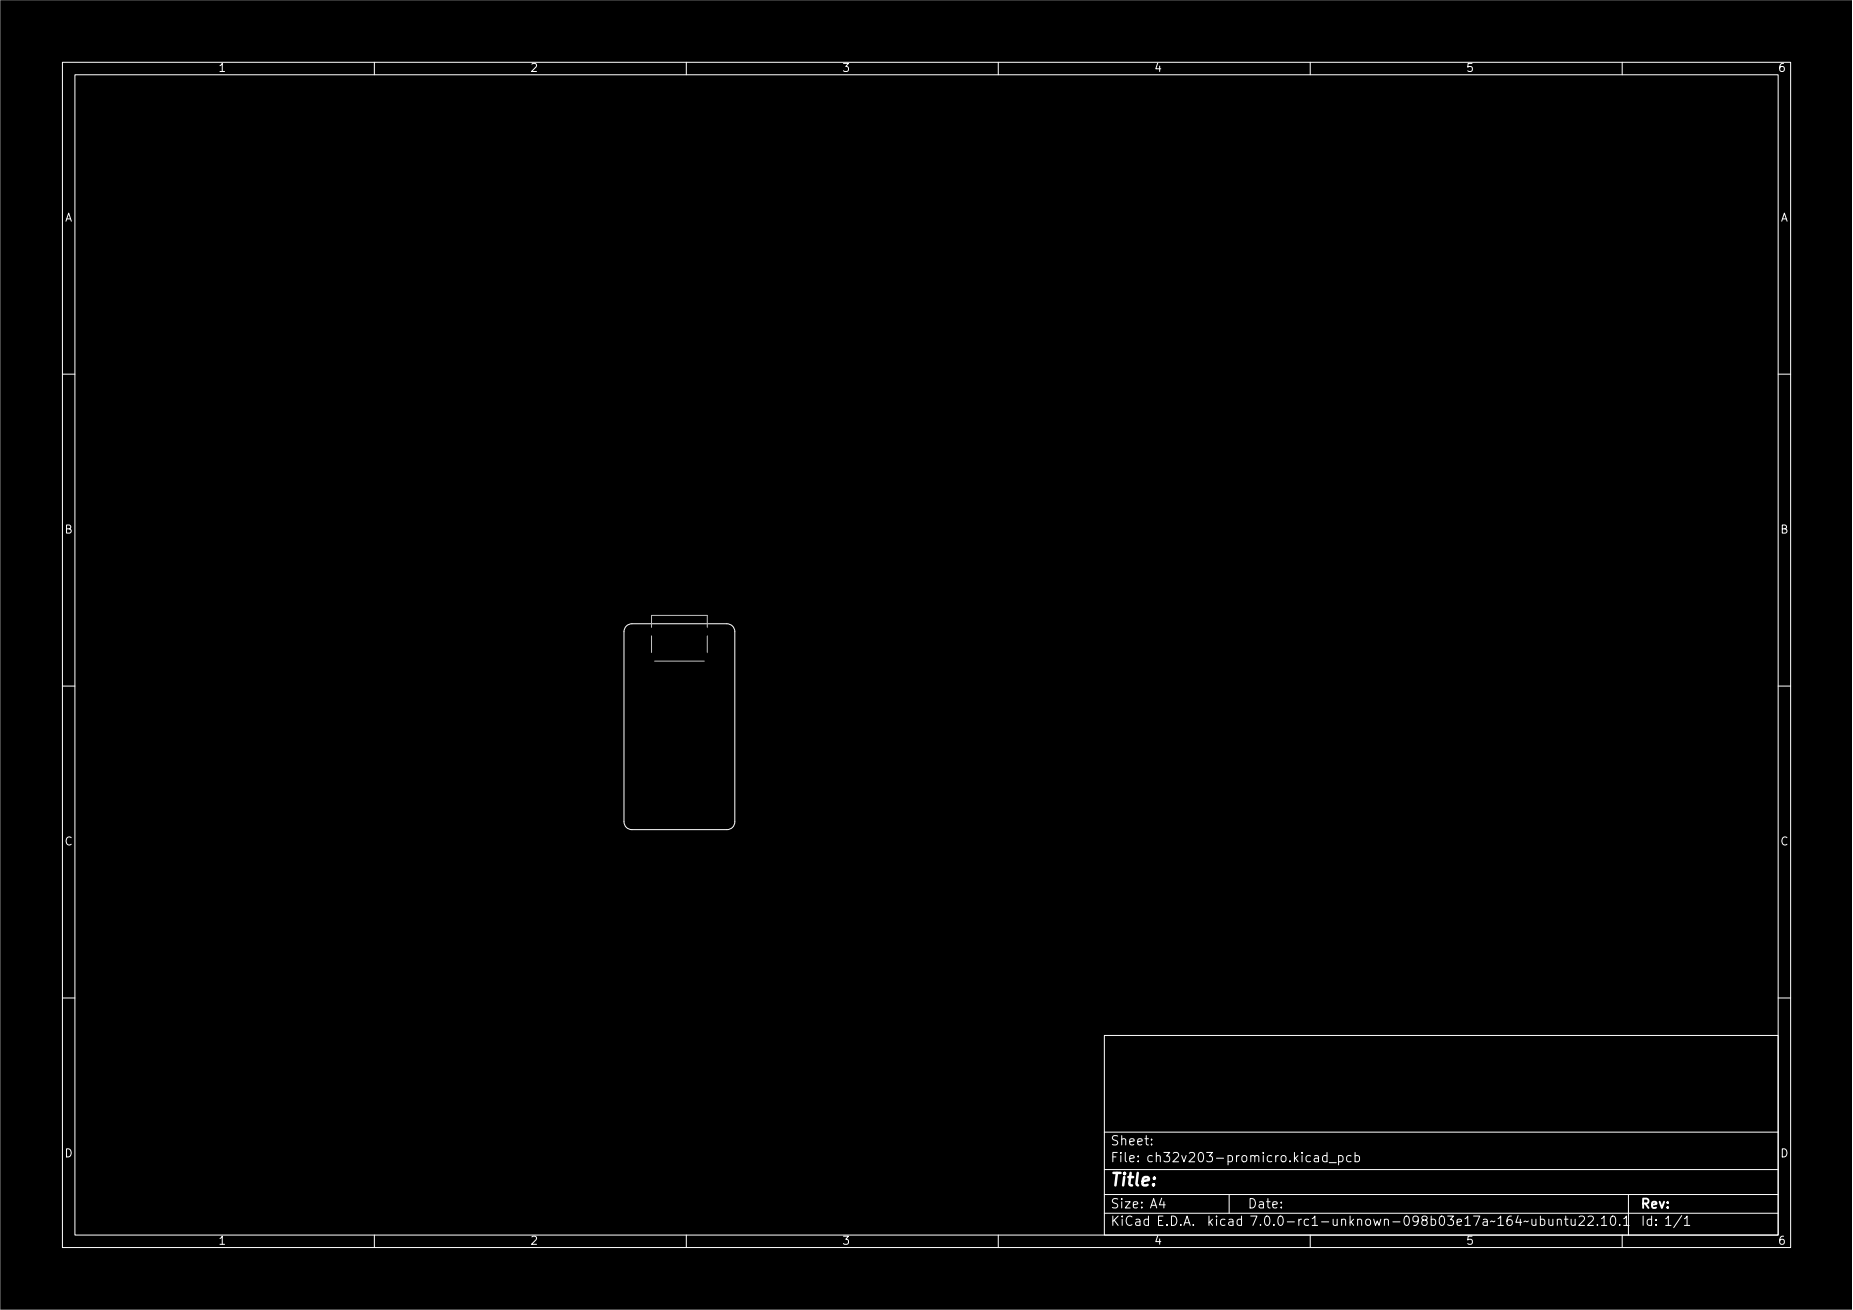
[picture p56: page 5]

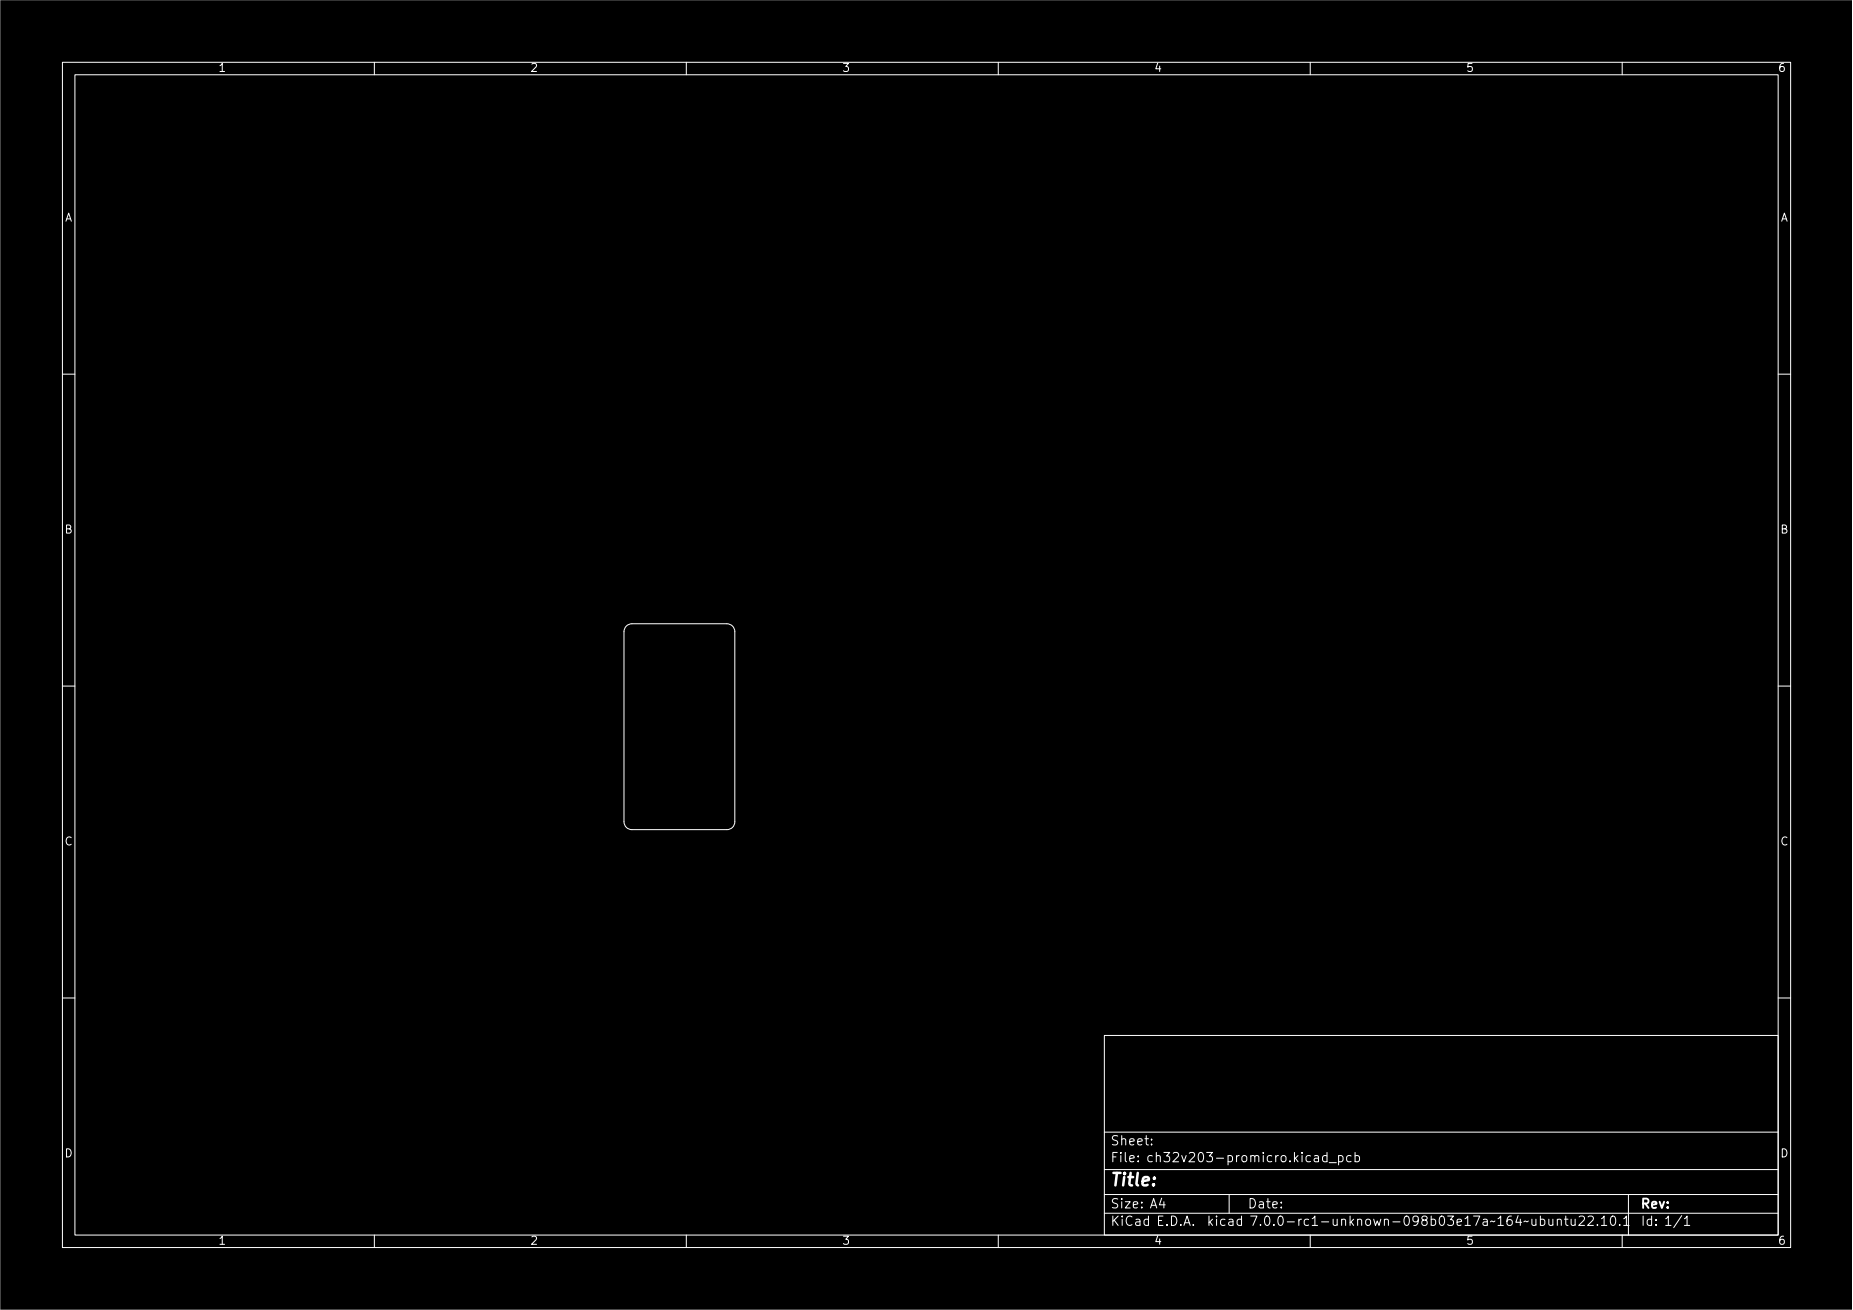
[picture p57: page 6]
