74th/ch32v-dev-boards/ch32x035-promicro-usb-device/ch32x035-usb-device-v1.0.0.pdf

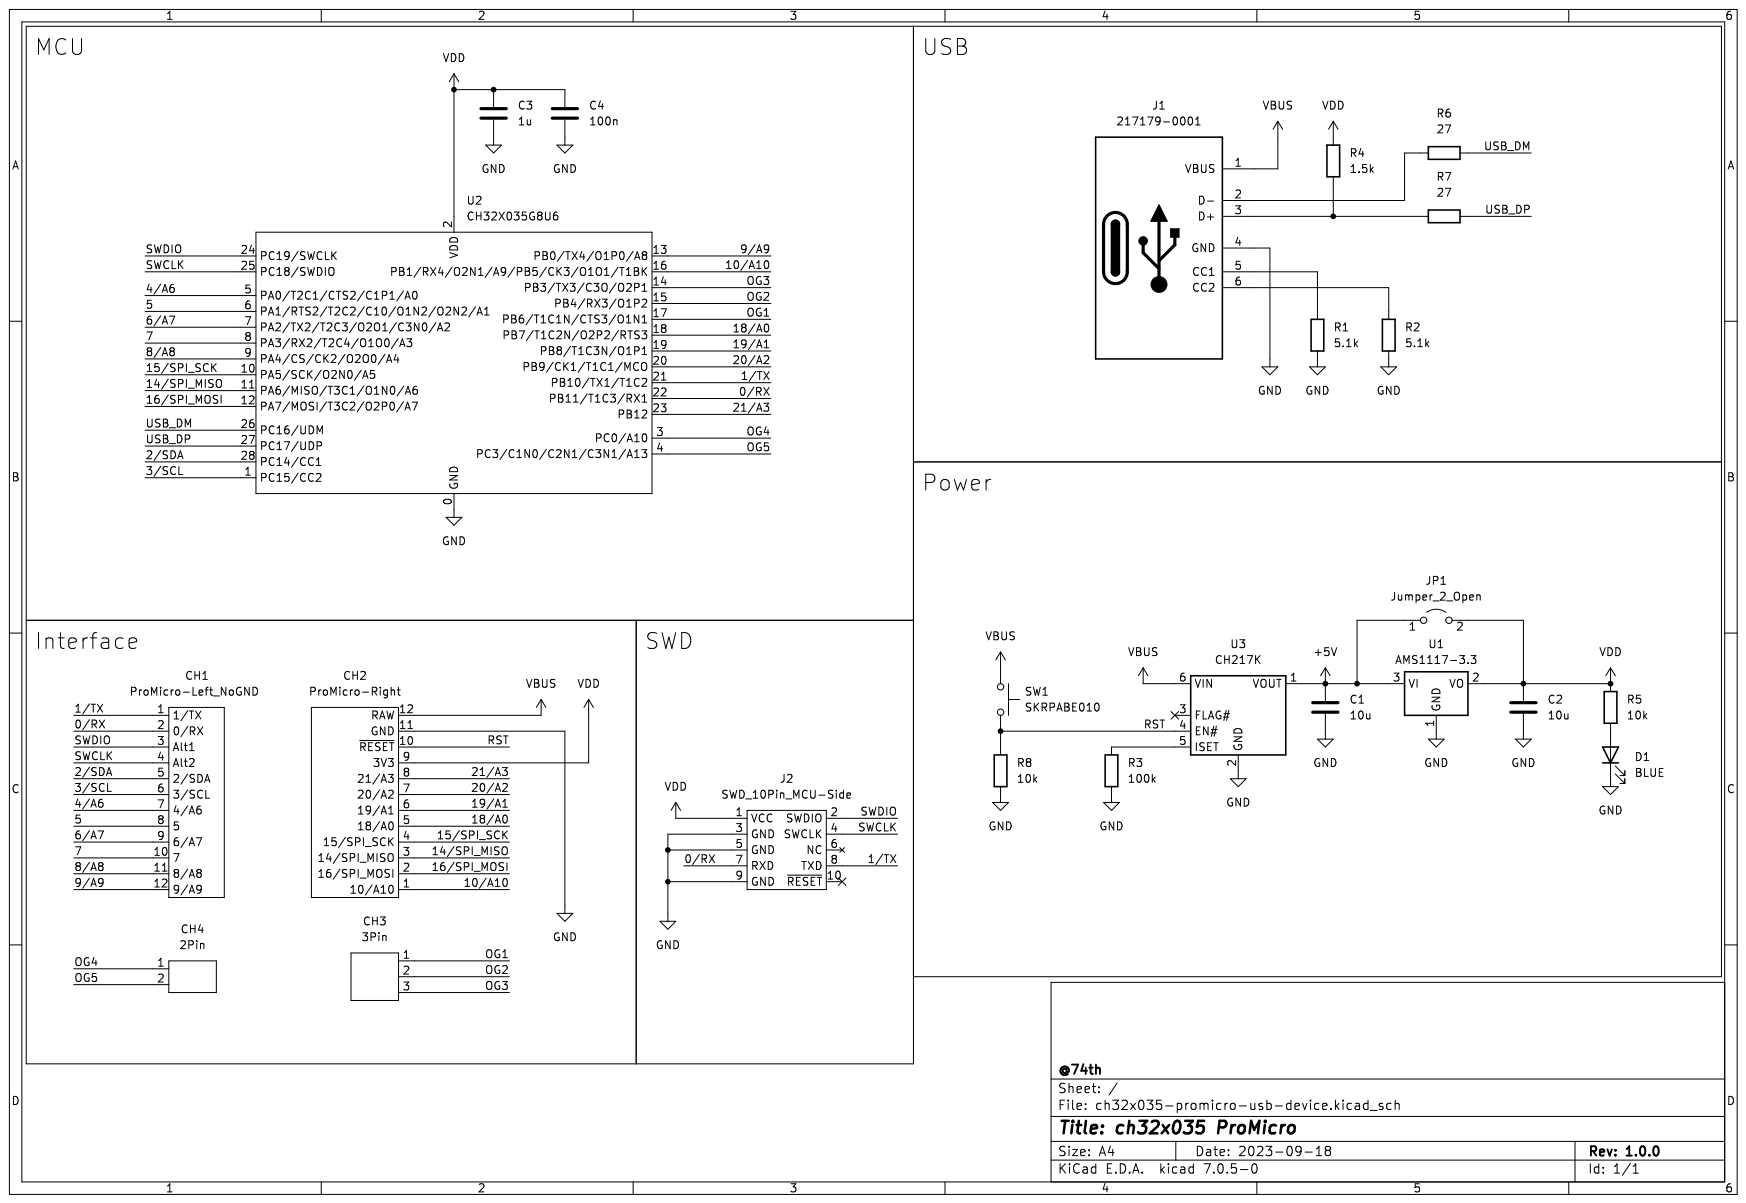
[picture p58: page 1]
