74th/ch32v-dev-boards/ch32v003-promicro/docs/ch32v003-promicro-semantics-v1.1.0.pdf

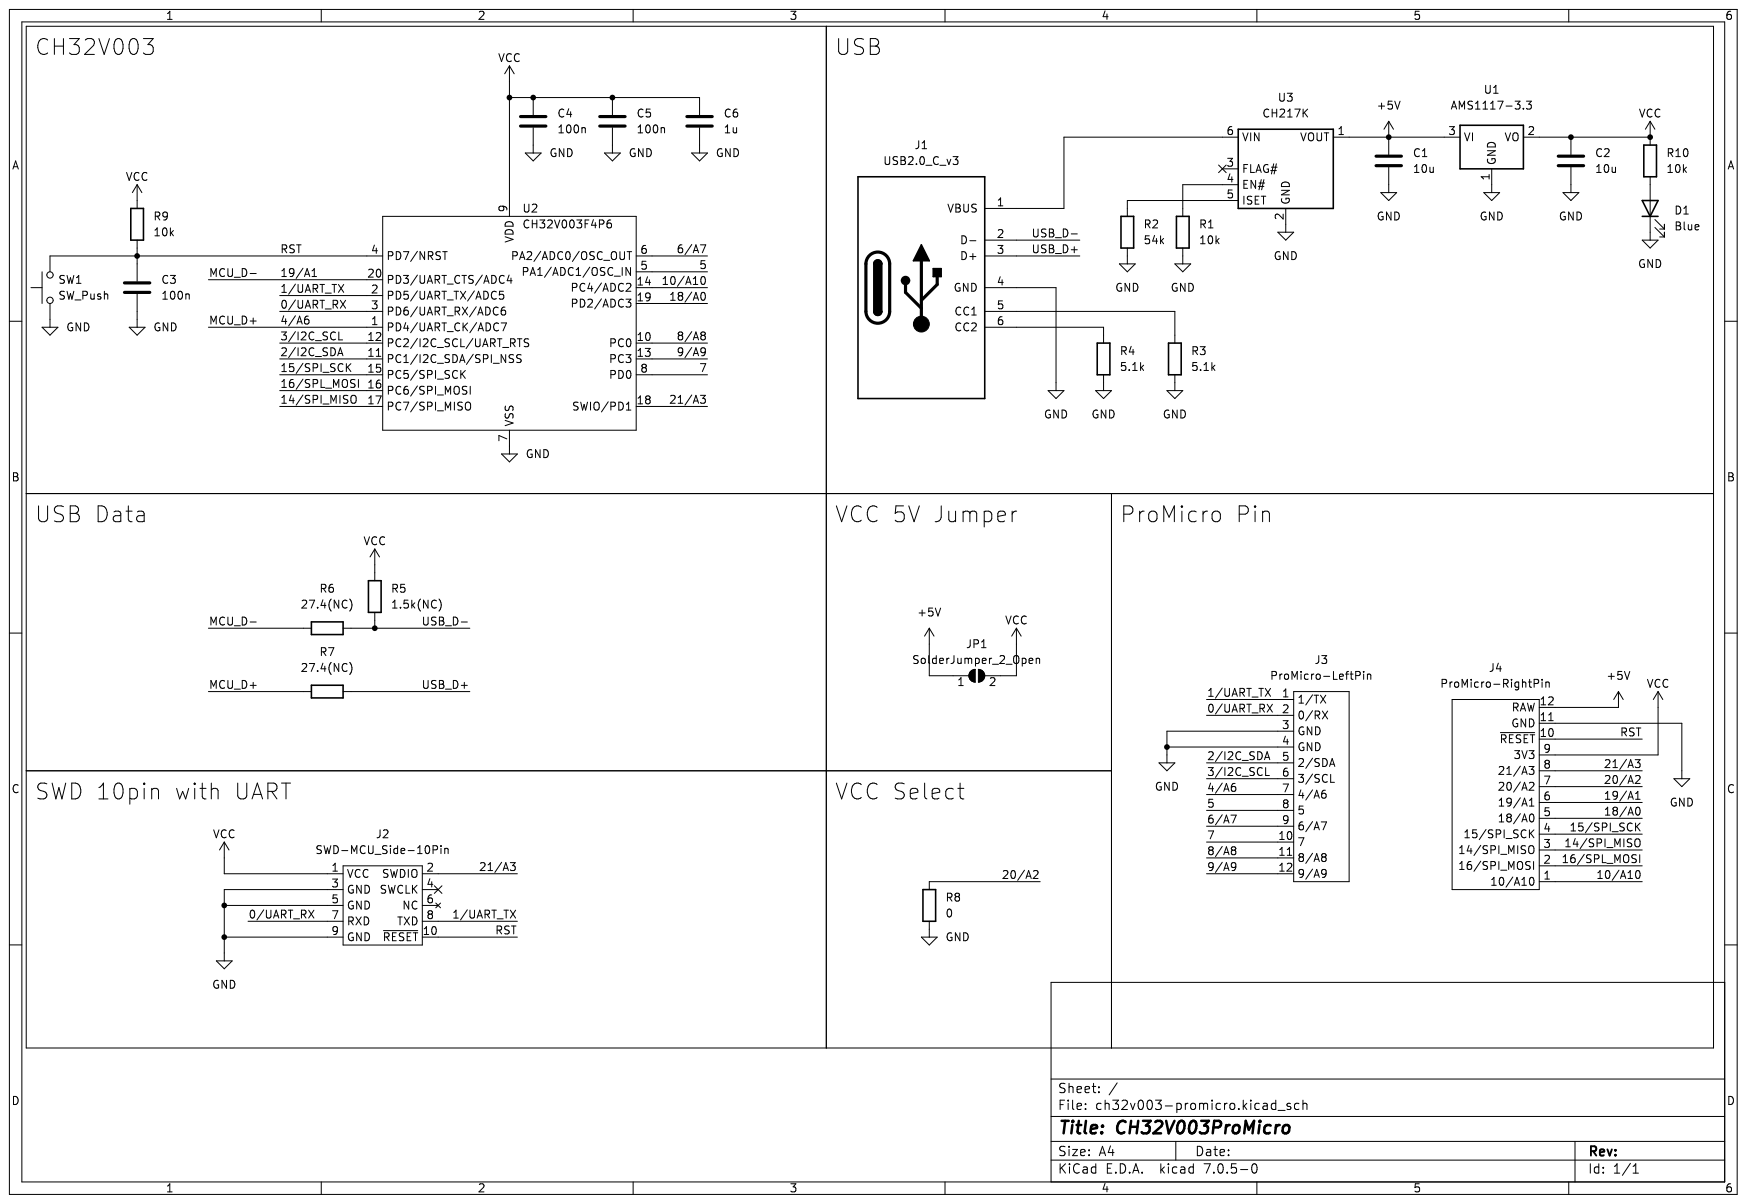
[picture p59: page 1]
