74th/ch32v-dev-boards/ch32v003-promicro/docs/ch32v003-promicro-semantics-v1.0.1.pdf

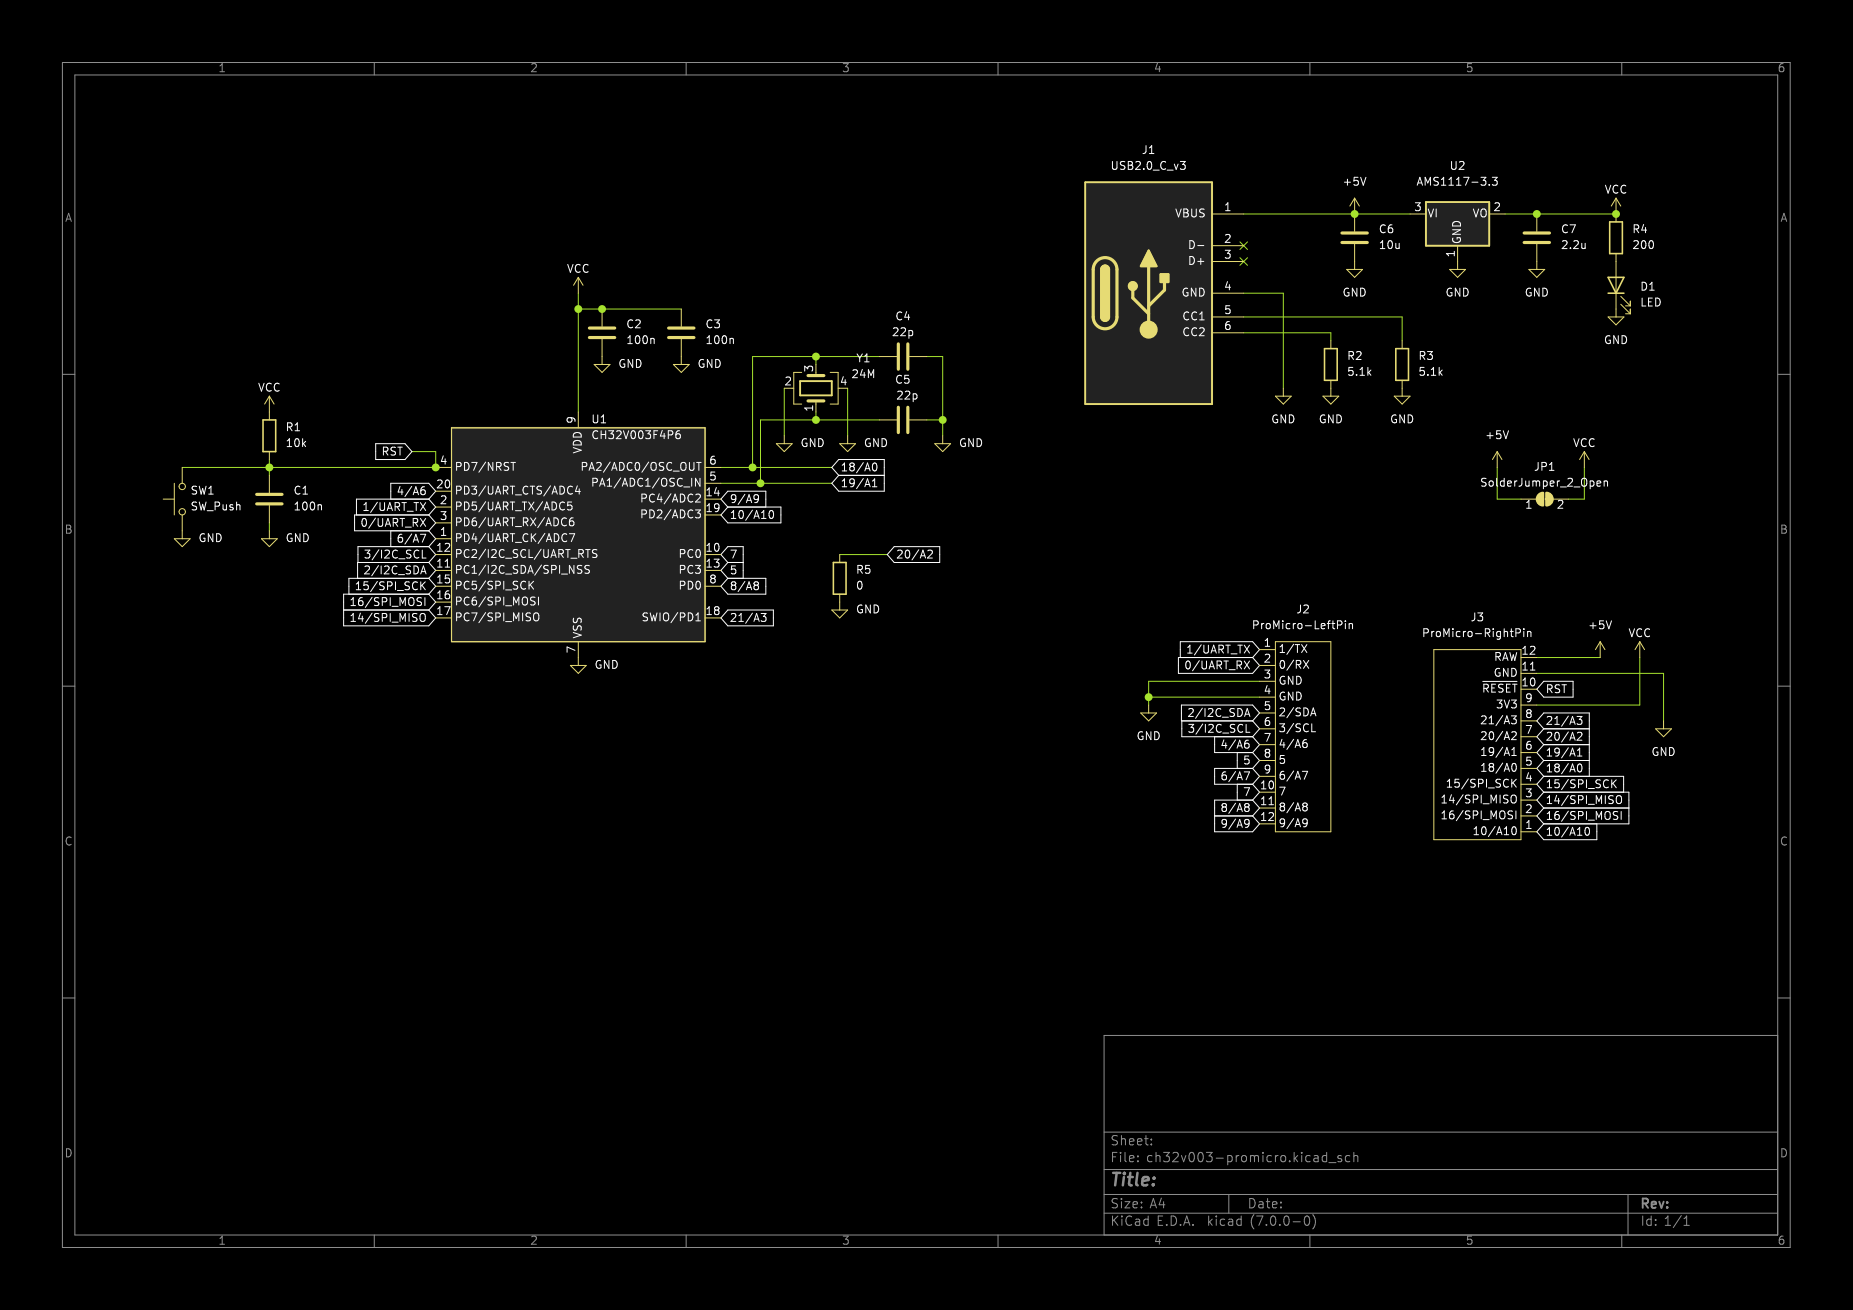
[picture p60: page 1]
