74th/ch32v-dev-boards/ch32v203-promicro/docs/ch32v203-promicro-v1.0.0-semantics.pdf

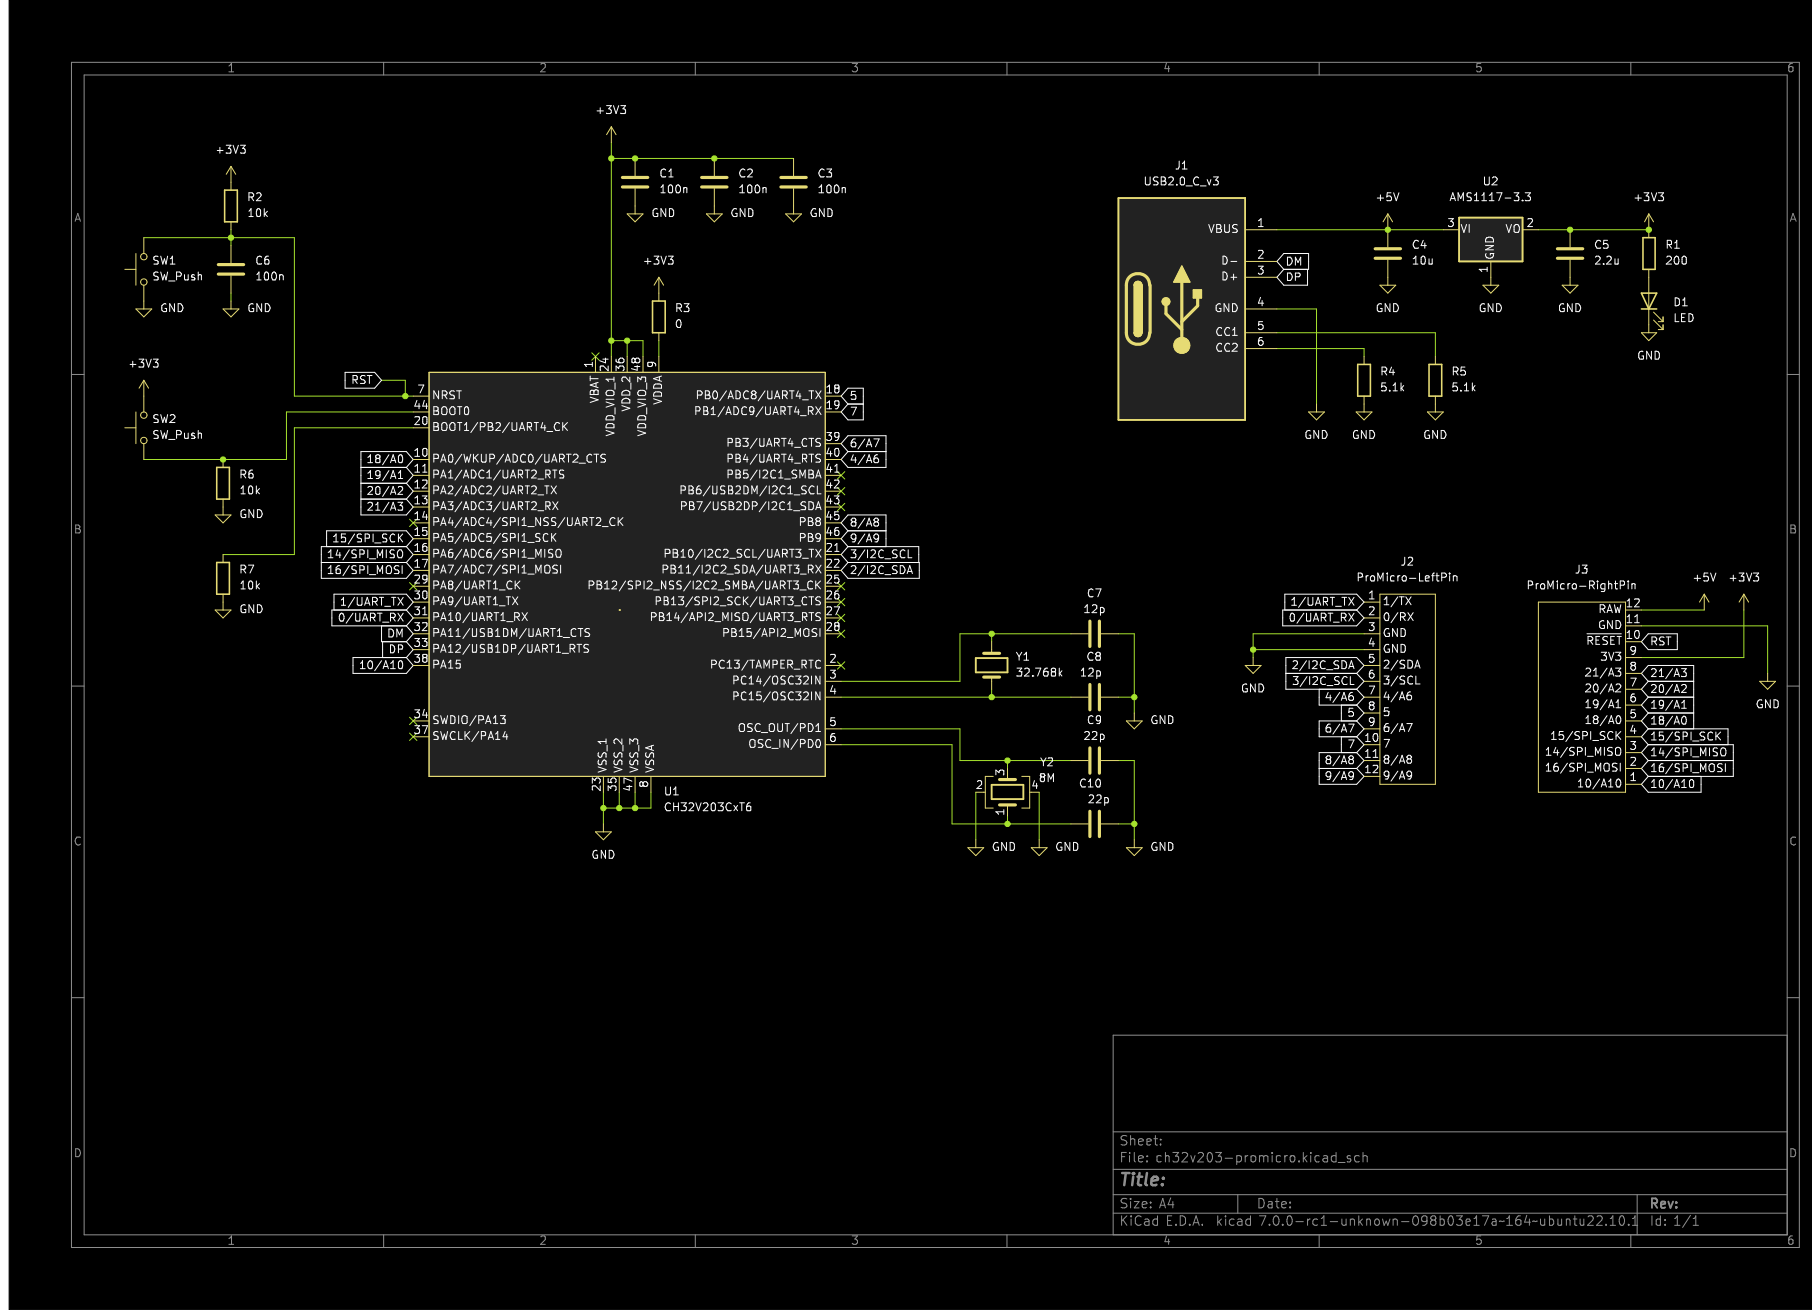
[picture p61: page 1]
